ok1hra/IC-705_Interface/wifilt.ino

/*
  Based on ESP32 BT CAT for IC-705 by OK1CDJ ondra@ok1cdj.com
  https://github.com/ok1cdj/IC705-BT-CIV
  -----------------------------------------------------------
  This program is free software: you can redistribute it and/or modify
  it under the terms of the GNU General Public License as published by
  the Free Software Foundation, either version 3 of the License, or
  (at your option) any later version.
  This program is distributed in the hope that it will be useful,
  but WITHOUT ANY WARRANTY; without even the implied warranty of
  MERCHANTABILITY or FITNESS FOR A PARTICULAR PURPOSE.  See the
  GNU General Public License for more details.
  You should have received a copy of the GNU General Public License
  along with this program.  If not, see <http://www.gnu.org/licenses/>.
  -----------------------------------------------------------

  Firmware build dependencies
  - Arduino IDE 1.8.19 or 2.x
  - Espressif Arduino-ESP32 core 2.0.14
  - Board: "ESP32 Dev Module"
  - Partition Scheme: "No OTA (2MB APP/2MB SPIFFS)"
  - TrxNet 0.3.0: https://github.com/ok1hra/TrxNet
  EEPROM, BluetoothSerial, WiFi, ESPmDNS, WebServer, FS and LittleFS are
  supplied by the pinned ESP32 core; PubSubClient is not required.

  DATA/JS8 asset and release dependencies (Debian 12)
    sudo apt install build-essential ca-certificates cmake dpkg-dev emscripten \
      git gzip libboost1.81-dev libfftw3-dev nodejs p7zip-full python3 \
      terser xz-utils
  Enable matching Debian deb-src entries for the pinned FFTW source build.
  Reviewed release versions: Emscripten 3.1.6, CMake 3.25.1, Node 18.20.4
  (local checks accept Node 18-20). See docs/js8call-build.md.

  1. Increase REV value in this .ino
  2. Arduino IDE 1.8.19 menu: Sketch/Export compiled Binary (for "ESP32 Dev Module" + Tools/Partition Scheme:"No OTA (2MB APP/2MB SPIFFS)")
  3. ./tools/upload-firmware-spiffs.sh --port /dev/ttyUSB0
     check without write
     ./tools/upload-firmware-spiffs.sh --dry-run
    for slow comm
    ./tools/upload-firmware-spiffs.sh --port /dev/ttyUSB0 --baud 460800

  3. generate all .bin and publish to GitHub web page: $ ./tools/gh-pages.sh --publish
  4. git commit with comment Release number and push

  Manual workflow
  - afer standart edit data/*.html/css/js,
  - before manual filesystem upload run tools/gzip-assets.sh
  - continue with Arduino IDE

  Features
  + Three independently configured radio slots using LAN, TrxNet or CI-V
  + Frequency and mode for PHP log available on http port 81 (address http://wifilt.local:81)
  + UDP port 89 receives ascii characters and transmits them as a CW or RTTY message
  + UDP port 89 receives ascii characters, which it sends in RTTY mode by keying FSK and PTT TRX inputs
  + Status LED
    - Fade in/out - WiFi in AP mode
    - WiFi in client mode
      - ON waiting connected to WiFi
      - OFF Wifi connected to AP
      - FLASH send MQTT freq
      - DOUBLE FLASH receive CW via UDP
      - FLASH+PTT receive RTTY via UDP
  + mDNS - to easily find IP devices in the network, using the command "ping wifilt.local"
  + Watchdog - resets the device after more than 73 seconds of inactivity
  + Output signal POWER-OUT (13.8V/0.5A) with LED activates after connecting a full-CAT primary radio
  + Galvanically isolated CI-V output for connecting PA or other devices
  + CIV-MUTE on gpio16 allow send to CI-V output only commands with frequency (not debug messages)
  + UDP port for CAT command (clear RIT) from log
  + after a full-CAT primary connection, set TRX to enable CI-V transceive + RIT + BK-IN
  + support external shift register control switch by frequency (not tested)
  + Detect PCB hardware ID
  + postponed MQTT
  + legacy BT configuration retained only for downgrade compatibility
  + detect HW rev 02
  + after connect WiFi, play assigned IP address in CW on a full-CAT TRX1 as sidetone only (BK-IN forced off so it never transmits; snapshots+restores mode/BK-IN/AF/RF gain)
  + send ? in serial terminal, answer interface status
  + add AP mode - status LED signal AP mode by slowly turning on and off (fade in / fade out)
  + add setup http web form on port 80
  + add HW rev 3 detection
  + optional reset after diconnect
  + add Debug to CLI

  
  FYI https://github.com/Rhizomatica/mercury

//--------------------------------------------------------------------*/

String SSID         = "";
String PSWD         = "";
String SSID2        = "";
String PSWD2        = "";
// TrxNet config — NET_ID 0x00 = disabled sentinel (TrxNet not activated)
byte     TRXNET_ID      = 0x01;   // own device NET_ID → device name "705.01"
byte     TRX2_NET_ID    = 0xff;   // peer NET_ID for TRX2 Band Decoder slot (0x00 = disabled)
byte     TRX3_NET_ID    = 0x00;   // peer NET_ID for TRX3 Band Decoder slot (0x00 = disabled)
byte     TRX2_CONN_TYPE = 0x00;   // 0=TrxNet, 1=CI-V, 2=LAN (EEPROM byte 44)
byte     TRX3_CONN_TYPE = 0x00;   // 0=TrxNet, 1=CI-V, 2=LAN (EEPROM byte 47)
byte     TRX2_CIV_ADDR  = 0x00;   // CI-V address of TRX2 when CONN_TYPE=CI-V (EEPROM byte 48; 0x00=unset)
byte     TRX3_CIV_ADDR  = 0x00;   // CI-V address of TRX3 when CONN_TYPE=CI-V (EEPROM byte 49; 0x00=unset)
uint16_t TRXNET_PORT    = 5683;   // CoAP/discovery UDP port (CoAP default)
int BaudRate        = 9600;
// char* BTname        = "";
// const char* BTname  = "IC705-interface";
String BT_NAME;  // legacy EEPROM field, retained for downgrade compatibility
bool Debug          = false;
bool cwIpOnConnect  = true;       // announce WiFi IP via CW on first full-CAT radio connect
volatile bool cwIpSendPending = false;

#define LOOP_WARN_MS 200
#define REV 20260807
#define WIFI
#define UDP_TO_FSK
#define WDT         // watchdog timer
#define CIV_OUT     // send freq to CIV out with BaudRate
// #define BLUETOOTH   // legacy only; UI supports LAN, TrxNet and CI-V
// #define RTLE     // not work now | credit OK2CQR https://github.com/ok2cqr/rtle/tree/master
// #define RESET_AFTER_DISCONNECT  // enable reset after each disconnect + short CW msg

#include "EEPROM.h"
#define EEPROM_SIZE 360
/*
  0|Byte    1|128
  1|Char    1|A
  2|UChar   1|255
  3|Short   2|-32768
  5|UShort  2|65535
  7|Int     4|-2147483648
  11|Uint    4|4294967295
  15|Long    4|-2147483648
  19|Ulong   4|4294967295
  23|Long64  8|0x00FFFF8000FF4180
  31|Ulong64 8|0x00FFFF8000FF4180
  39|Float   4|1234.1234
  43|Double  8|123456789.12345679
  51|Bool    1|1

  0 APmode
  1-20 SSID1
  22-39 PSWD1
  41 TRXNET_ID       (own NET_ID, 0x00=disabled → device name "705.XX")
  42 TRX2_NET_ID     (peer NET_ID for TRX2 BD slot, 0x00=disabled)
  43 TRX3_NET_ID     (peer NET_ID for TRX3 BD slot, 0x00=disabled)
  44 TRX2_CONN_TYPE (0=TrxNet, 1=CI-V, 2=LAN; 0xff=unprogrammed → default 0x00)
  45-46 TRXNET_PORT  (was MQTT_PORT)
  47 TRX3_CONN_TYPE (0=TrxNet, 1=CI-V, 2=LAN; 0xff=unprogrammed → default 0x00)
  48 TRX2_CIV_ADDR  (CI-V address of TRX2; 0x00/0xff = unset)
  49 TRX3_CIV_ADDR  (CI-V address of TRX3; 0x00/0xff = unset)
  50 TRX1_CONFIG_MARKER (0xa5=current; 0xff=legacy memories.cfg fallback)
  51 TRX1_TRANSPORT  (1=LAN, 2=legacy Bluetooth, 3=CI-V, 4=TrxNet)
  52 TRX1_CIV_ADDR
  53-68 TRX1_LAN_IP (16B including 0xff terminator padding)
  69 FREE            (was HTTP_CAT_PORT)
  70-71 FREE         (was udpPort)
  72-73 FREE         (was udpCatPort)
  74-75 BaudRate
  76-95 SSID2
  97-114 PSWD2
  115-131 TRX1_LAN_USER (17B including 0xff terminator padding)
  132-135 FREE       (was MQTT_TOPIC_RX)
  136 cwIpOnConnect
  137-200 DXC host (64B)
  201-202 DXC port (UShort)
  203-218 DXC callsign (16B)
  219-224 DXC locator (6B)
  225-241 TRX1_LAN_PASSWORD (17B including 0xff terminator padding)
  242-245 FREE       (was TRX2 MQTT root topic)
  246-266 FREE       (was TRX3 MQTT root topic 21B)
  267-287 BT_NAME (21B)
  288 TRXNET_PRIO flag (0xff=unprogrammed → default "OI3 ANT"; 0x01=user set → read string)
  289-359 TRXNET_PRIO priority prefixes string (space-separated, 71B; empty = priority off)

  !! Increment EEPROM_SIZE #define !!
*/

#if defined(BLUETOOTH)
  #include "BluetoothSerial.h"
  #include <esp_bt.h>
#endif
  //#define DEBUG 1
  //#define MIRRORCAT 1
  //#define MIRRORCAT_SPEED 9600
  // CI-V protocol constants and radio state below are shared by every transport
  // (Bluetooth SPP and LAN both feed processCivBuffer), so they compile
  // unconditionally. Only the BluetoothSerial object is Bluetooth-specific.
  #define BROADCAST_ADDRESS    0x00 //Broadcast address
  #define CONTROLLER_ADDRESS   0xE0 //Controller address

  #define START_BYTE           0xFE //Start byte
  #define STOP_BYTE            0xFD //Stop byte

  #define CMD_TRANS_FREQ       0x00 //Transfers operating frequency data
  #define CMD_TRANS_MODE       0x01 //Transfers operating mode data

  #define CMD_READ_FREQ        0x03 //Read operating frequency data
  #define CMD_READ_MODE        0x04 //Read operating mode data

  #define CMD_WRITE_FREQ       0x05 //Write operating frequency data
  #define CMD_WRITE_MODE       0x06 //Write operating mode data

  #define CMD_SEND_CW_MSG      0x17 //Write operating mode data

  #define IF_PASSBAND_WIDTH_WIDE   0x01
  #define IF_PASSBAND_WIDTH_MEDIUM   0x02
  #define IF_PASSBAND_WIDTH_NARROW   0x03

  const uint32_t decMulti[]    = {1000000000, 100000000, 10000000, 1000000, 100000, 10000, 1000, 100, 10, 1};

  #define BAUD_RATES_SIZE 4
  const uint16_t baudRates[BAUD_RATES_SIZE]       = {19200, 9600, 4800, 1200};

  uint8_t  radio_address;     //Transiever address
  uint16_t  baud_rate;        //Current baud speed
  uint32_t readtimeout = 2000;
  uint8_t  read_buffer[12];   //Read buffer
  // uint8_t  read_buffer_snapshot[12];   //Buffer snapshot
  uint32_t  frequency;        //Current frequency in Hz
  uint32_t  frequencyTmp;        //Current frequency in Hz
  uint32_t  timer;

  const char* mode[] = {"LSB", "USB", "AM", "CW", "FSK", "FM", "WFM", "DV"};
  #define MODE_TYPE_LSB   0x00
  #define MODE_TYPE_USB   0x01
  #define MODE_TYPE_AM    0x02
  #define MODE_TYPE_CW    0x03
  #define MODE_TYPE_RTTY  0x04
  #define MODE_TYPE_FM    0x05
  #define MODE_TYPE_DV    0x17

  char modes[12] = "OFF";
  // btClientConnected stays declared unconditionally: state/status JSON reads it
  // even without Bluetooth (it simply remains false when BT is compiled out).
  volatile bool btClientConnected = false;
#if defined(BLUETOOTH)
  BluetoothSerial CAT;
#endif

short HardwareRev = 99;
const int HWidPin       = 34;  // analog
int HWidValue           = 0;

int pwmChannel          = 0; // Selects channel 0
int frequence           = 1000; // PWM frequency of 1 KHz
int resolution          = 8; // 8-bit resolution, 256 possible values

const int StatusPin     = 5;
const int PowerOnPin    = 4;
long powerTimer         = 0;
bool statusPower        = 0;
const int CIVmutePin    = 16;
bool TrxNeedSet         = 0;
bool TrxSetupDone       = false;
volatile bool btStateBroadcastPending = false;
volatile bool btDisconnectPending = false;
volatile bool btConnectPending = false;

#if defined(WDT)
  // 73 seconds WDT (WatchDogTimer)
  #include <esp_task_wdt.h>
  #define WDT_TIMEOUT 73
  long WdtTimer=0;
#endif

#if defined(WIFI)
  #include <WiFi.h>
  #include <esp_wifi.h>
  #include "esp_coexist.h"
  #include <FS.h>
  #include <LittleFS.h>
  #define HTTP_MAX_DATA_WAIT 1000
  #include <WebServer.h>
  #include <mbedtls/sha1.h>
  #include <lwip/sockets.h>   // raw select() to poll audio-WS writability (never block the loop)
  // #include <ETH.h>
  // int SsidPassSize = (sizeof(SsidPass)/sizeof(char *))/2; //array size
  // int SelectSsidPass = -1;
  #define wifi_max_try 40             // Number of try
  unsigned long WifiTimer = 0;
  unsigned long WifiReconnect = 5000;
  unsigned long WifiDownSince = 0;        // 0 = station link OK
  bool WifiHardResetDone = false;         // one radio off/on per outage — repeating it wedges the driver
  bool WifiCoexPreferred = false;         // coex arbiter tilted to WiFi for the duration of an outage
  #define WIFI_HARD_RESET_AFTER_MS 10000  // radio off/on cycle when down longer than this
  #define WIFI_RESTART_AFTER_MS    60000  // ESP.restart() when down longer than this
  // Last known AP — reconnect targets channel+BSSID directly, because a full
  // scan often finds nothing while the BT Classic (SPP) link is active (coex).
  int32_t wifiLastChannel = 0;
  uint8_t wifiLastBssid[6];
  bool    wifiLastBssidValid = false;
  String  wifiLastSsid;
  unsigned long webQuietUntil = 0;
  byte ActiveWifiProfile = 0;
  String MACString;

  #include <ESPmDNS.h>
  #include <DNSServer.h>

  const char* ssidAP     = "WIFILT-AP";
  const char* passwordAP = "remoteqth";
  // One name for three lookup paths: the DHCP hostname the router registers in
  // its own DNS (http://wifilt/), the mDNS name (http://wifilt.local) and the AP
  // captive portal. Keeping them identical is the whole point -- the operator
  // types one string no matter which mechanism their network actually supports.
  const char* deviceHostname = "wifilt";
  bool APmode = false;
  // WebServer discards the client before handleClient() returns, so the slow-loop
  // diagnostic can't sample it from outside. Response writes (where stalls to a dead
  // client block the loop) go through this virtual, so capture peer+uri here.
  class DiagWebServer : public WebServer {
  public:
    using WebServer::WebServer;
    IPAddress lastPeer;
    String lastUri;
  protected:
    size_t _currentClientWrite(const char* b, size_t l) override {
      if (_currentClient.connected()) {
        lastPeer = _currentClient.remoteIP();
        lastUri = _currentUri;
      }
      return WebServer::_currentClientWrite(b, l);
    }
  };
  DiagWebServer webServer(80);
  const byte DNS_PORT = 53;
  DNSServer dnsServer;             // captive portal in AP mode
#endif
  #if defined(RTLE)
    #ifndef HTTP_MAX_DATA_WAIT
      #define HTTP_MAX_DATA_WAIT 1000
    #endif
    #include <WebServer.h>
    #include "rtle.h"  //Web page header file
    WebServer rtleserver(88);
  #endif


// uint8_t CwMsg[36] = "";
char CwMsg[37] = "";

#if defined(UDP_TO_FSK)
  #define FSK_OUT  33                      // TTL LEVEL pin OUTPUT
  #define PTT      32                      // PTT pin OUTPUT
  #define FSK_MARK_LEVEL   LOW             // FSK mark level [LOW/HIGH]
  #define FSK_SPACE_LEVEL  HIGH            // FSK space level [LOW/HIGH]
  #define BaudRateFSK 45.45                   // RTTY baud rate
  #define StopBit  1.5                     // stop bit long
  #define PTTlead  400                     // PTT lead delay ms
  #define PTTtail  200                     // PTT tail delay ms
  int     OneBit = 1/BaudRateFSK*1000;
  boolean d1;
  boolean d2;
  boolean d3;
  boolean d4;
  boolean d5;
  boolean space;
  boolean fig1;
  int     fig2;
  char    ch;
  volatile bool abortFskTransmission = false;
#endif


// TrxNet — P2P telemetry, replaces PubSubClient/MQTT
// TRXNET_ID == 0x00 acts as "disabled" sentinel — net.begin() is not called.
// NOTE: never #define TRXNET_MAX_PENDING/TRXNET_MAX_PEERS here — TrxNet.cpp is
// compiled separately without sketch defines, so the class layout would differ
// between translation units (ODR violation → global memory corruption → boot
// crash in first nvs_open). Library per-board defaults apply (ESP32: 24).
#include <WiFiUdp.h>
#include <TrxNet.h>
#include "icomLanClient.h"      // LAN CI-V transport (alternative to BT)
#include "radio_transport.h"    // shared per-slot transport/capability model
#include "aud1_tx_state.h"      // shared TX-state predicates used by native regression tests
#include "unattended_guard.h"   // shared liveness/arming rules used by native regression tests
#include "unattended_events.h"  // shared event-log formatting used by native regression tests
#include "aud1_ws_parser.h"     // incremental, non-blocking browser WebSocket framing
#include "js8_session.h"        // single-operator lock for the JS8LAN page
IcomLanClient lanClient;
IcomLanClient* secondaryLanClients[2] = {nullptr, nullptr};
bool    lanMode = true;         // compatibility mirror: TRX1 transport == LAN
String  lanRadioIp = "";        // radio IP for LAN mode
String  lanUser = "";           // ICOM network username
String  lanPass = "";           // ICOM network password
uint32_t lanFreqTmp = 0;        // last freq published to TrxNet (change detect)
bool    lanReconnectRequested = false;
uint32_t lanRetryAt = 0;
uint32_t lanBackoff = 3000;

// ---- LAN radio discovery (SETUP page) -------------------------------------
// The scanner and the credential test both need UDP 50001, which the live LAN
// client owns. WiFiUDP sets SO_REUSEADDR, so a second bind succeeds and then
// silently steals the client's control packets -- the live client is therefore
// stopped for the duration and reconnected afterwards, never run alongside.
#include "icom_lan_discovery.h"
IcomLanDiscovery icomScan;
enum IcomScanPhase : uint8_t {
  ISCAN_IDLE, ISCAN_SUSPEND, ISCAN_RUN,
  ISCAN_TEST_SUSPEND, ISCAN_TEST_RUN,
  ISCAN_DONE
};
IcomScanPhase icomScanPhase = ISCAN_IDLE;
bool     icomScanSuspendLan = false;   // gate honoured by the LAN service loops
bool     icomScanLanWasUp = false;     // reconnect afterwards only if we cut it
bool     icomScanFailed = false;       // scan could not start (no station link)
IcomLanClient* icomTestClient = nullptr;
IPAddress icomTestIp;
String   icomTestUser, icomTestPass;
uint8_t  icomTestCivAddr = 0xA4;
uint8_t  icomTestSlot = 0;             // which TRX slot the tested address belongs to
String   icomTestModel;                // model the radio reported during the test
uint32_t icomTestDeadline = 0;
const char* icomTestResult = "idle";   // idle|running|ok|bad_credentials|no_answer

// ---- AP -> station handoff --------------------------------------------------
// Saving WiFi credentials in AP mode used to end with a blind restart: the
// portal vanished and the operator was left with no address to open. Instead
// the station is brought up alongside the still-running softAP, so the portal
// can show the address the router actually handed out before the AP goes away.
#define LAST_STA_IP_ADDR 132       // EEPROM 132-135, previously MQTT_TOPIC_RX
// One configured WiFi profile as the scan actually saw it on the air.
struct WifiScanPick {
  byte    profile = 0xFF;
  int32_t rssi = -127;
  int32_t channel = 0;
  uint8_t bssid[6] = {0};
  bool    targeted = false;   // false = no scan hit, connect the ordinary way
};
enum WifiTryState : uint8_t { WTRY_IDLE, WTRY_SCAN, WTRY_CONNECTING, WTRY_OK, WTRY_FAILED };
WifiTryState wifiTryState = WTRY_IDLE;
uint32_t  wifiTryDeadline = 0;
String    wifiTrySsid;
const char* wifiTryReason = "";    // not_found | no_connect, when state == failed
WifiScanPick wifiTryCandidates[2]; // profiles to attempt, strongest scan hit first
uint8_t   wifiTryCandidateCount = 0;
uint8_t   wifiTryCandidateIdx = 0;
bool      wifiTryScanSawNothing = false;  // a scan completed and found no configured SSID
IPAddress lastStaIp;               // survives a reboot; 0.0.0.0 when unknown

static const char* RADIO_CONFIG_PATH = "/radio-config.json";

struct RadioSlotConfig {
  bool enabled;
  RadioTransport transport;
  uint8_t civAddr;
  uint8_t netId;
  String lanIp;
  String lanUser;
  String lanPass;
  // Model the radio reported in its capabilities packet, remembered across
  // reboots. Not operator-editable -- it is an observation, not a setting.
  // WSPR needs it to know whether 100 % of the CI-V power scale means 10 W or
  // 100 W, and without a stored copy that answer disappears with the link.
  String model;
};

RadioSlotConfig radioSlots[3];
bool radioConfigLoaded = false;
bool primarySerialHasData = false;
bool primaryTrxNetHasData = false;
uint32_t secondaryLanRetryAt[2] = {0, 0};
uint32_t secondaryLanBackoff[2] = {3000, 3000};

// ── The LAN radio, wherever the operator put it ───────────────────────────────
// LAN may be assigned to any one of the three slots, and JS8LAN (audio, PTT, TX)
// follows it instead of assuming TRX1. The shared CAT globals (frequency, modes,
// stateTx, meters) belong to TRX1 -- /state, the log page's TRX1 tab, band
// decoder source 1 and the TrxNet publish all read them -- so a LAN radio in
// slot 1 or 2 keeps its own compact snapshot here and the JS8 page asks for it
// with /state?radio=lan. Only one slot can be LAN, hence one snapshot.
struct LanRadioSnapshot {
  uint8_t  slot = 0xFF;           // which slot this snapshot describes
  bool     tx = false;
  uint8_t  filter = 0;
  uint8_t  rfPower = 0;
  bool     rfPowerSeen = false;   // false until the radio answered 14 0A at least once
  uint16_t smeterRaw = 0;
  uint16_t powerMeterRaw = 0;
  // Raw ALC, and a counter that only moves when the radio actually answered
  // 15 13. The browser's gain search cannot tell a fresh reading from the
  // previous one repeated -- and mistaking one for the other makes it step
  // twice on a single observation -- so the sequence, not the value, is what
  // says "this is new". Deliberately absent from /state: it is only meaningful
  // while the browser is keying, and that is exactly when tx-level is flowing.
  uint16_t alcRaw = 0;
  uint32_t alcSeq = 0;
  float    swr = 1.0f;
  float    supplyVolts = 0.0f;
  char     mode[8] = "";          // includes the -D suffix, unlike g_trxMode
};
LanRadioSnapshot lanRadioSnap;
WiFiUDP trxUdp;
TrxNet  net(trxUdp);
char    trxDeviceName[TRXNET_MAX_DEVICE_NAME];
bool    trxNetEnabled = false; // set true after net.begin() succeeds

// TrxNet priority prefixes — protect these peers when the peer table fills.
// EEPROM 288 flag + 289-359 string. Limits: 8 tokens x 8 chars (see setPriorityPrefixes()).
#define TRXNET_PRIO_MAX_TOKENS 8
#define TRXNET_PRIO_MAX_TOKLEN 8
#define TRXNET_PRIO_STR_MAX    71   // 8*8 + 7 separators
String      TRXNET_PRIO = "OI3 ANT";                 // canonical (normalized) value for UI/save
char        trxPrioBuf[TRXNET_PRIO_STR_MAX + 1];     // tokenized: spaces -> '\0' (library holds a pointer)
const char* trxPrioPtrs[TRXNET_PRIO_MAX_TOKENS];     // pointers into trxPrioBuf, valid for object lifetime
uint8_t     trxPrioCount = 0;

// TrxNet pending state — set in callbacks, processed in loop()
volatile uint32_t trxPendingHz   = 0;
volatile uint8_t  trxPendingMode = 0; // CI-V byte
volatile bool     trxFreqPending = false;
volatile bool     trxModePending = false;

int incomingByte = 0;   // for incoming serial data

#if defined(WIFI)
  WiFiServer dxcRawServer(82);
  WiFiClient DxcTelnetClient;
  WiFiClient DxcWsClient;
  WiFiServer audioWsServer(83);        // AUD1 WebSocket: timed RX/TX audio for DATA page
  WiFiClient AudioWsClient;
  uint32_t audioRxPackets = 0;         // counts forwarded audio datagrams per WS session
  uint8_t  audioTxBuf[1400];           // coalesce ~20ms radio packets into fewer WS frames
  size_t   audioTxLen = 0;
  // Outgoing browser-WS byte ring. RX audio is enqueued here (even from the LAN
  // UDP receive path) and drained with non-blocking ::send, so no WS write ever
  // blocks the cooperative loop and the LAN-UDP owner never performs a socket
  // send. ~2 s at 8 kB/s absorbs transient browser/WiFi stalls before dropping.
  // Heap-allocated in setup() — too large for the static DRAM (.bss) segment.
  static const size_t WS_OUT_SIZE = 16384;
  uint8_t* wsOut = nullptr;
  size_t   wsOutHead = 0, wsOutTail = 0, wsOutLen = 0;
  bool     audioTxKeyed = false;       // M3: PTT keyed for browser-sourced TX audio
  bool     audioPttOffPending = false; // desired OFF not yet submitted to healthy CI-V
  uint32_t audioPttRetryAt = 0;
  uint32_t audioTxLastMs = 0;          // last TX audio/keep-alive — dead-man un-key timer
  uint32_t audioStreamId = 0;          // changes for every WebSocket media epoch
  uint32_t audioRxSequence = 0;
  uint64_t audioRxFirstSample = 0;
  bool audioRxFirst = true;
  bool audioRxDiscontinuity = false;
  bool audioRadioSequenceValid = false;
  uint16_t audioRadioExpectedSequence = 0;

  Aud1TxState aud1TxState = AUD1_TX_IDLE;
  static const size_t AUD1_TX_RING_SIZE = IcomLanAudioTx::QUEUE_CAPACITY;
  size_t aud1TxUsed = 0;                    // atomic snapshot mirror for UI/state JSON
  uint32_t aud1TxId = 0, aud1TxExpectedSequence = 0, aud1TxExpectedPackets = 0;
  uint32_t aud1TxReceivedPackets = 0, aud1TxTargetMs = 0;
  uint32_t aud1TxDeadlineMs = 0, aud1TxPrebufferSamples = 0;
  uint64_t aud1TxExpectedSample = 0, aud1TxTotalSamples = 0, aud1TxConsumedUlaw = 0;
  bool aud1TxLastSeen = false;
  Aud1WsParser aud1WsParser;
  UnattendedGuard unattendedGuard;
  Js8Session js8Session;                   // which browser currently owns JS8LAN
  static const char* UNATTENDED_LOG_PATH = "/unattended.log";
  // Deferred unattended-log ring. unattendedLogEvent() is called from the audio
  // hot path (aud1TxAbort/aud1TxTick/aud1HandleControl); a synchronous LittleFS
  // append+rotate there is a multi-100 ms flash stall that can miss the very next
  // JS8 slot. Events are formatted into this RAM ring instead and flushed to flash
  // only from loop() while no TX is imminent (unattendedLogFlush). Heap-allocated
  // like wsOut; if malloc fails, the hot path records an overflow marker and
  // still never falls back to a synchronous flash write during TX.
  static const size_t UNA_LOG_QUEUE_SIZE = 2048;   // ~17 lines of <=120 B
  uint8_t* unaLogQueue = nullptr;
  size_t   unaLogHead = 0, unaLogTail = 0, unaLogLen = 0;
  bool     unaLogOverflow = false;                 // oldest lines dropped since last flush
  // MSG BOX: store-and-forward mail, unread mail for the operator and our own
  // deferred outgoing messages, one typed record per line. Decision 10 keeps it
  // here rather than in the tab so it survives a reload, a different computer
  // and a cleared browser cache, and can be read from a phone. 96 messages x
  // ~120 chars fits well inside the 256 KiB runtime reserve the deployment gate
  // keeps free.
  static const char* MSGBOX_PATH = "/msgbox.jsonl";
  // Pre-type file. Read once so mail survives the upgrade, then removed; the
  // browser is what knows how to tell the old record kinds apart.
  static const char* MSGBOX_LEGACY_PATH = "/inbox.jsonl";
  static const size_t MSGBOX_MAX_BYTES = 24576;
  bool lanLinkWasUp = false;               // LAN link-up edge for the PTT safety un-key
  uint32_t aud1TxLevelNextMs = 0;          // B3: periodic TX buffer level while streaming
  // Survives a WDT/panic reset (not power loss) so a reset that happened with
  // the radio keyed is reportable instead of silent.
  RTC_NOINIT_ATTR uint32_t rtcPttWasKeyed;
  static const size_t AUD1_WS_RX_BYTE_BUDGET = 32768; // yield even when browser continuously streams
  static const uint32_t AUD1_WS_SLOT_BACKLOG_GRACE_MS = 100;
  String DxcHost = "";
  uint16_t DxcPort = 7300;
  IPAddress DxcHostIp;                // cached resolve — hostByName blocks the loop for seconds
  String DxcHostResolved = "";        // host the cache belongs to
  #define DXC_CONNECT_TIMEOUT_MS 1500
  String DxcCallsign = "";
  String DxcLocator = "";

  static const char* LOG_CONFIG_PATH = "/log-config.json";

  // Measured ALC knees, one entry per model|band|percent. Deliberately opaque
  // to the firmware: it serves the file and overwrites it, and never parses a
  // byte of it. The schema belongs to the browser, which is the only party that
  // can decide what a calibration means -- and a parser here would be a second
  // opinion about it, needing RAM, a version field and a migration path for a
  // table the radio itself has no use for.
  //
  // Firmware-side rather than in localStorage because the knee is a property of
  // the station -- radio, band, power -- not of the browser that measured it. An
  // unattended beacon started from a phone must not transmit at a level that was
  // only ever calibrated on the shack PC.
  static const char* TXGAIN_CONFIG_PATH = "/txgain.json";
  static const size_t TXGAIN_MAX_BYTES = 6144;   // ~40 entries; a full band plan

  // In-memory cache of log-config.json fields used by setupTemplateProcessor.
  String g_lcTrx1Label = "TRX1";   // replaced by the radio's own model once known
  String g_lcTrx2Label = "TRX2";
  String g_lcTrx3Label = "TRX3";
  String g_lcRstSsb    = "59";
  String g_lcRstCwRtty = "599";
  bool   g_lcManualModeForPhone = true;
  String g_lcBlockedDxcc = "Russia\nBelarus\nKaliningrad";

  // TrxNet peer cache for TRX2 (index 0) and TRX3 (index 1) — written by onHz/onMode callbacks
  static volatile long g_trxFreq[2]    = {0, 0};
  static char          g_trxMode[2][8] = {"USB", "USB"};
  static volatile bool g_trxHasData[2] = {false, false};

// Band Decoder
#define BD_CLOCK_PIN  15
#define BD_LATCH_PIN  13
#define BD_DATA_PIN   14
#define BD_ROWS       16
#define BD_CONFIG_PATH "/bd-config.json"

struct BdRow {
    uint32_t fMin;
    uint32_t fMax;
    uint16_t outputs;
};

BdRow     bdRows[BD_ROWS];
int       bdSource         = 1;
uint16_t  bdCurrentOutputs = 0;
bool      bdEnabled        = false;

  bool DxcTelnetStatus = false;
  bool DxcWsStatus = false;
  bool DxcTelnetLoginPending = false;
  unsigned long DxcReconnectTimer = 0;
#endif

#if defined(WIFI)
typedef mbedtls_sha1_context SHA1_CTX;

extern "C" void SHA1Init(SHA1_CTX* context){
  mbedtls_sha1_init(context);
  mbedtls_sha1_starts_ret(context);
}

extern "C" void SHA1Update(SHA1_CTX* context, const unsigned char* data, uint32_t len){
  mbedtls_sha1_update_ret(context, data, len);
}

extern "C" void SHA1Final(unsigned char digest[20], SHA1_CTX* context){
  mbedtls_sha1_finish_ret(context, digest);
  mbedtls_sha1_free(context);
}
#endif

#if defined(WIFI)
  const uint8_t CW_MEMORY_COUNT = 4;
  const uint8_t FREQ_MEMORY_COUNT = 10;
  const size_t CW_MEMORY_MAX_LEN = 30;
  const size_t FREQ_MEMORY_MAX_LEN = 20;
  const uint8_t CIV_ADDRESS_DEFAULT = 0xA4;
  const char *MEMORY_CONFIG_PATH = "/memories.cfg";
  const uint8_t PRIMARY_RADIO_CONFIG_MARKER = 0xA5;
  const int PRIMARY_RADIO_MARKER_ADDR = 50;
  const int PRIMARY_RADIO_TRANSPORT_ADDR = 51;
  const int PRIMARY_RADIO_CIV_ADDR = 52;
  const int PRIMARY_RADIO_LAN_IP_ADDR = 53;
  const int PRIMARY_RADIO_LAN_USER_ADDR = 115;
  const int PRIMARY_RADIO_LAN_PASS_ADDR = 225;
  // BT CAT poll cadence (used by pollRadio) — slow when idle, fast while the
  // CAT page holds it via /state?fast=1
  #define CAT_POLL_MS       1000  // slow: freq poll interval
  #define CAT_MODE_EVERY    2     // slow: mode polled every N-th freq tick (2 s)
  #define AUX_POLL_MS       160   // slow: aux round-robin step (each of 10 items every 1.6 s)
  #define CAT_POLL_FAST_MS  200   // fast: freq+mode poll interval (original cadence)
  #define AUX_POLL_FAST_MS  80    // fast: aux round-robin step
  #define CAT_FAST_HOLD_MS  3000  // fast mode lingers this long after the last ?fast=1 poll
  #define CAT_POLL_OUTAGE_MS 3000 // WiFi outage: freq-only poll — BT must go near-silent
                                  // so the SPP link can sniff and WiFi can re-associate
  unsigned long catFastUntil = 0;
  String setupSsidErr = "";
  String setupPswdErr = "";
  String setupSsid2Err = "";
  String setupPswd2Err = "";
  String setupCivAddrErr = "";
  bool setupSaveOk = false;
  String transceiverType = "ICOM-LAN";  // LAN is the recommended default (BT deprecated)
  uint8_t configuredCivAddress = CIV_ADDRESS_DEFAULT;
  String cwMemoryText[CW_MEMORY_COUNT];
  String freqMemoryText[FREQ_MEMORY_COUNT];
  portMUX_TYPE stateMux = portMUX_INITIALIZER_UNLOCKED;

  // State variables updated from CIV frames, served via /state polling
  uint32_t stateRitRaw = 0;
  uint8_t stateFilter = 1;
  uint8_t stateAfGain = 0;
  uint8_t stateKeySpeed = 138;
  // 205 is a fabricated default, not a reading. Pages that turn the level into
  // watts must not present it as one, so say plainly whether the radio has ever
  // answered 14 0A -- the snapshot below carries the same flag for TRX2/TRX3,
  // where the equally fabricated default is 0.
  uint8_t stateRfPower = 205;
  bool stateRfPowerSeen = false;
  bool stateTx = false;
  uint8_t statePreampMode = 0;  // 0=OFF, 1=AMP, 2=ATT
  uint8_t stateAttOn = 0;       // internal: tracks ATT separately for combine logic
  uint8_t stateVoxMode = 0;
  uint8_t stateRfGain = 0;      // 0x14 0x02 RF gain, needed to snapshot/restore around CW IP announce
  uint8_t stateModeId = 0x03;   // numeric operating-mode id (0x03=CW), for exact mode restore
  bool    stateDataMode = false;// DATA sub-mode flag, so USB-D/etc. restore correctly
  float stateSupplyVolts = 0.0f;
  float stateSwr = 1.0f;
  uint32_t stateSmeterRaw = 0;
  uint32_t statePowerMeterRaw = 0;
  // TRX1's ALC, with the same freshness counter as the snapshot's. Two copies
  // because a LAN radio on TRX1 feeds the shared CAT globals and never the
  // snapshot -- see lanCivFrameRoute(), which returns early for slot 0.
  uint32_t stateAlcRaw = 0;
  uint32_t stateAlcSeq = 0;

  // civ.read: the one CI-V reply a page asked for, kept as RAW HEX. Nothing here
  // decodes it -- the same discipline as /txgain.json, which this firmware stores
  // and never parses. A settings value like 1A 05 01 17 is BCD on one model and
  // an enumeration on the next, so the only honest place for the meaning is the
  // page that asked. Zero RAM for a parser, and no model knowledge in C++.
  //
  // Absence is the answer for an address the radio does not have: no reply means
  // civReadSeq never moves, and the caller reports "the radio did not confirm
  // that address" instead of writing to it. See docs/tx-audio-gain-plan-*.md.
  static const size_t CIV_READ_MAX = 16;
  uint8_t  civReadPrefix[CIV_READ_MAX] = {0};   // cmd + subaddress bytes to match
  uint8_t  civReadPrefixLen = 0;
  uint8_t  civReadReply[CIV_READ_MAX] = {0};   // cmd + payload of the matching frame
  uint8_t  civReadReplyLen = 0;
  uint32_t civReadSeq = 0;
  uint32_t civReadAtMs = 0;

  String requestArg(const char *name);
  bool requestHasArg(const char *name);
  String trimMemoryValue(const String &value, size_t maxLen);
  bool parseHexByteString(const String &value, uint8_t &outValue);
  void loadMemoryConfig(void);
  bool saveMemoryConfig(void);
  bool hasPrimaryRadioConfig(void);
  void loadPrimaryRadioConfig(void);
  bool savePrimaryRadioConfig(void);
  void initLegacyRadioSlots(void);
  bool loadRadioConfig(void);
  bool saveRadioConfig(void);
  void syncLegacyRadioGlobals(void);
  bool radioSlotConnected(uint8_t slot);
  void radioSlotSetFrequencyState(uint8_t slot, uint32_t freq);
  void radioSlotSetModeState(uint8_t slot, const char *mode);
  IcomLanClient* radioLanClient(uint8_t slot);
  bool beginRadioLanClient(uint8_t slot);
  void secondaryLanClientsLoop(void);
  uint8_t lanRadioSlotIndex(void);
  String defaultTrxLabel(uint8_t slot);
  void adoptModelAsLabelIfUnset(uint8_t slot);
  IcomLanClient* lanRadioClient(void);
  bool lanRadioConnected(void);
  bool lanRadioSendCommand(const uint8_t *body, size_t len);
  bool lanRadioSendPriorityCommand(const uint8_t *body, size_t len, IcomLanClient::CivPriority priority);
  void lanRadioAudioService(IcomLanClient *client);
  void lanRadioCivSnapshot(const uint8_t *frame, size_t len);
  void lanCivFrameRoute(uint8_t slot, const uint8_t *frame, size_t len);
  String jsonEscape(const String &value);
  String configJsonEscape(const String &s);
  String civFrameToHex(const uint8_t *frame, size_t frameLen);
  uint32_t decodeCivFrequencyBytes(const uint8_t *bytes, size_t byteCount);
  uint32_t decodeCivBcdBytes(const uint8_t *bytes, size_t byteCount);
  String decodeModeName(uint8_t modeId);
  bool catWriteFrame(const uint8_t *frame, size_t frameLen, bool broadcastTx);
  bool catWriteFrameSlot(uint8_t slot, const uint8_t *frame, size_t frameLen);
  void setModesText(const char *value);
  void copyModesText(char *dest, size_t destSize);
  bool applyModeState(uint8_t modeId, bool dataMode);
  String extractJsonString(const String &json, const char *key);
  String extractJsonObject(const String &json, const char *key);
  bool extractJsonBool(const String &json, const char *key, bool defaultValue);
  bool parseHexPayload(const String &hex, uint8_t *buffer, size_t &bufferLen, size_t maxLen);
  bool parseModeId(const String &modeName, uint8_t &modeId);
  uint8_t parseFilterWidth(const String &filterName);
  size_t buildSimpleCatFrame(uint8_t command, const uint8_t *payload, size_t payloadLen, uint8_t *frame, size_t frameMaxLen);
  size_t buildSetFrequencyFrame(uint32_t freqHz, uint8_t *frame, size_t frameMaxLen);
  size_t buildSetModeFrame(uint8_t modeId, uint8_t modeWidth, uint8_t *frame, size_t frameMaxLen);
  size_t buildReadQuickSplitFrame(uint8_t *frame, size_t frameMaxLen);
  void buildStateJson(char *buf, size_t bufSize, bool lanView);
  void handleGetState(void);
  bool sendTemplatedHtml(const char *path);
  void handleSetupData(void);
  void handleTrxNetPeers(void);
  void handleWebServerLoop(void);
  bool handleFileFromSPIFFS(const String &path);
  void handlePostCmd(void);
  void handleSet(void);
  void renderSetupPage(void);
  void resetSetupMessages(void);
  String setupTemplateProcessor(const String &key);
  void setupWebServer(void);
  void handleConfigDownload(void);
  void handleConfigUpload(void);
  void handleGetLogConfig(void);
  void handlePostLogConfig(void);
  void handleGetTxGain(void);
  void handlePostTxGain(void);
  void handleGetCivRead(void);
  void civReadArm(const uint8_t *prefix, size_t prefixLen);
  void civReadCapture(const uint8_t *frame, size_t len);
  void handleOi3State(void);
  void handleOi3Send(void);
  void handleOi3SetHz(void);
  void TrxNetLoop(void);
  void onTrxHz(const char* from, const uint8_t* data, size_t len);
  void onTrxMode(const char* from, const uint8_t* data, size_t len);
  void onTrxSetHz(const char* from, const uint8_t* data, size_t len);
  static const char* trxnetModeToString(uint8_t civMode);
  void lanSecondaryCivFrameHandler(uint8_t slot, const uint8_t *frame, size_t len);
  static void civSend(uint8_t toAddr, const uint8_t* body, size_t bodyLen);
  void DxcLoop(void);
  void dxcHandleRawClient(void);
  bool DxcConfigReady(void);
  void DxcDisconnectTelnet(void);
  void DxcDisconnectWebSocket(void);
  void DxcRequestReconnect(void);
  void DxcUpdateTelnetStatus(bool connected, bool forceSend = false);
  void DxcSendTelnetStatus(void);
  bool DxcConnectTelnet(void);
  bool WiFiStationReady(void);
  void WiFiRetryActiveProfile(const char *reason);
  bool DxcSendWebSocketFrame(uint8_t opcode, const uint8_t* payload, size_t length);
  bool DxcSendWebSocketText(const char* text);
  bool DxcSendWebSocketText(const String& text);
  bool DxcHandleWebSocketUpgrade(WiFiClient& webClient, const String& request);
  void DxcHandleWebSocketClient(void);
  void DxcHandleTelnetClient(void);
  String ExtractHttpHeader(const String& request, const String& headerName);
  String DxcComputeWebSocketAccept(const String& secKey);
  String Base64Encode(const uint8_t* data, size_t length);
  bool AudioSendBinary(const uint8_t* payload, size_t length);
  bool AudioSendText(const String& text);
  void wsRingReset(void);
  void audioDrainWs(void);
  void audioFlush(void);
  void audioPttOn(void);
  void audioPttOff(void);
  void audioPttSafetyOnLink(void);
  void audioPttSafetyRetryTick(void);
  void unattendedLogEvent(uint8_t type, const String& detail);
  void unattendedLogEnqueue(const char* line, size_t n);
  void unattendedLogFlush(void);
  bool txCriticalNow(void);
  bool txRealtimeNow(void);
  void handleUnattendedGet(void);
  void handleUnattendedPost(void);
  void handleUnattendedLog(void);
  void js8SessionRespond(Js8SessionResult result, const String& token);
  String js8SessionRequestToken(void);
  void handleJs8SessionGet(void);
  void handleJs8SessionClaim(void);
  void handleJs8SessionPing(void);
  void handleJs8SessionRelease(void);
  void handleMsgboxGet(void);
  void handleMsgboxPost(void);
  void aud1TxAbort(const String& reason, bool notify = true);
  void aud1TxTick(bool deferPrebufferMiss = false);
  void AudioDisconnectWs(void);
  bool AudioHandleWsUpgrade(WiFiClient& webClient, const String& request, const String& token);
  void AudioHandleWsClient(void);
  void audioHandleRawClient(void);
#endif

//-------------------------------------------------------------------------------------------------------

#if defined(WIFI)
String requestArg(const char *name){
  return webServer.arg(name);
}

bool requestHasArg(const char *name){
  return webServer.hasArg(name);
}

String trimMemoryValue(const String &value, size_t maxLen){
  String trimmed = value;
  trimmed.trim();
  if (trimmed.length() > maxLen) {
    trimmed = trimmed.substring(0, maxLen);
    trimmed.trim();
  }
  return trimmed;
}

bool parseHexByteString(const String &value, uint8_t &outValue){
  String normalized = value;
  normalized.trim();
  normalized.toUpperCase();
  if (normalized.startsWith("0X")) {
    normalized = normalized.substring(2);
  }
  if (normalized.length() == 0 || normalized.length() > 2) {
    return false;
  }

  char buffer[3] = {0, 0, 0};
  normalized.toCharArray(buffer, sizeof(buffer));
  char *endPtr = nullptr;
  long parsed = strtol(buffer, &endPtr, 16);
  if (endPtr == nullptr || *endPtr != '\0' || parsed < 0 || parsed > 255) {
    return false;
  }
  outValue = (uint8_t)parsed;
  return true;
}

void loadMemoryConfig(void){
  for (uint8_t i = 0; i < CW_MEMORY_COUNT; i++) {
    cwMemoryText[i] = "";
  }
  for (uint8_t i = 0; i < FREQ_MEMORY_COUNT; i++) {
    freqMemoryText[i] = "";
  }

  if (!LittleFS.exists(MEMORY_CONFIG_PATH)) {
    return;
  }

  File file = LittleFS.open(MEMORY_CONFIG_PATH, FILE_READ);
  if (!file) {
    return;
  }

  for (uint8_t i = 0; i < CW_MEMORY_COUNT && file.available(); i++) {
    cwMemoryText[i] = trimMemoryValue(file.readStringUntil('\n'), CW_MEMORY_MAX_LEN);
  }
  for (uint8_t i = 0; i < FREQ_MEMORY_COUNT && file.available(); i++) {
    freqMemoryText[i] = trimMemoryValue(file.readStringUntil('\n'), FREQ_MEMORY_MAX_LEN);
  }

  if (file.available()) {
    String configuredType = trimMemoryValue(file.readStringUntil('\n'), 16);
    if (configuredType == "IC-7610-CI-V" || configuredType == "TRXNET") {
      transceiverType = configuredType;
    } else {
      // Bluetooth transport removed: any stored non-CIV value falls back to LAN.
      transceiverType = "ICOM-LAN";
    }
  }

  if (file.available()) {
    uint8_t parsedAddress = CIV_ADDRESS_DEFAULT;
    if (parseHexByteString(file.readStringUntil('\n'), parsedAddress)) {
      configuredCivAddress = parsedAddress;
    }
  }

  // LAN transport config (backward compatible: absent lines -> empty)
  if (file.available()) lanRadioIp = trimMemoryValue(file.readStringUntil('\n'), 15);
  if (file.available()) lanUser    = trimMemoryValue(file.readStringUntil('\n'), 16);
  if (file.available()) lanPass    = trimMemoryValue(file.readStringUntil('\n'), 16);

  lanMode = (transceiverType == "ICOM-LAN");

  file.close();
}

bool saveMemoryConfig(void){
  File file = LittleFS.open(MEMORY_CONFIG_PATH, "w");
  if (!file) {
    Serial.println("LFS | cannot open /memories.cfg for writing"
                   " used=" + String(LittleFS.usedBytes()) +
                   " total=" + String(LittleFS.totalBytes()));
    return false;
  }

  size_t expectedBytes = 0;
  size_t writtenBytes = 0;
  auto writeLine = [&](const String &line) {
    expectedBytes += line.length() + 2;  // println uses CRLF
    writtenBytes += file.println(line);
  };

  for (uint8_t i = 0; i < CW_MEMORY_COUNT; i++) {
    writeLine(trimMemoryValue(cwMemoryText[i], CW_MEMORY_MAX_LEN));
  }
  for (uint8_t i = 0; i < FREQ_MEMORY_COUNT; i++) {
    writeLine(trimMemoryValue(freqMemoryText[i], FREQ_MEMORY_MAX_LEN));
  }
  writeLine(transceiverType);
  String civAddressLine;
  if (configuredCivAddress < 16) {
    civAddressLine = "0";
  }
  civAddressLine += String(configuredCivAddress, HEX);
  writeLine(civAddressLine);
  writeLine(lanRadioIp);
  writeLine(lanUser);
  writeLine(lanPass);

  file.flush();
  size_t fileBytes = file.size();
  bool ok = writtenBytes == expectedBytes && fileBytes == expectedBytes;
  file.close();
  if (!ok) {
    Serial.println("LFS | write failed for /memories.cfg expected=" +
                   String(expectedBytes) + " written=" + String(writtenBytes) +
                   " size=" + String(fileBytes) +
                   " used=" + String(LittleFS.usedBytes()) +
                   " total=" + String(LittleFS.totalBytes()));
  }
  return ok;
}

// Parse log-config.json into g_lc* variables so setupTemplateProcessor can serve them.
void loadLogConfigVars(void){
  if (!LittleFS.exists(LOG_CONFIG_PATH)) return;
  File f = LittleFS.open(LOG_CONFIG_PATH, "r");
  if (!f) return;
  String j = f.readString();
  f.close();
  j.trim();
  if (!j.startsWith("{")) return;

  String v;
  v = extractJsonString(j, "trx1Label"); if (v.length() > 0) g_lcTrx1Label = v;
  v = extractJsonString(j, "trx2Label"); if (v.length() > 0) g_lcTrx2Label = v;
  v = extractJsonString(j, "trx3Label"); if (v.length() > 0) g_lcTrx3Label = v;
  v = extractJsonString(j, "rstSsb");    if (v.length() > 0) g_lcRstSsb = v;
  v = extractJsonString(j, "rstCwRtty"); if (v.length() > 0) g_lcRstCwRtty = v;
  if (j.indexOf("\"blockedDxcc\"") >= 0) g_lcBlockedDxcc = extractJsonString(j, "blockedDxcc");
  g_lcManualModeForPhone = extractJsonBool(j, "manualModeForPhone", true);
}

String jsonEscape(const String &value){
  String out;
  out.reserve(value.length() + 8);
  for (size_t i = 0; i < value.length(); i++) {
    char c = value.charAt(i);
    switch (c) {
      case '\\': out += "\\\\"; break;
      case '"': out += "\\\""; break;
      case '\n': out += "\\n"; break;
      case '\r': out += "\\r"; break;
      case '\t': out += "\\t"; break;
      default: out += c; break;
    }
  }
  return out;
}

String civFrameToHex(const uint8_t *frame, size_t frameLen){
  String hex;
  hex.reserve(frameLen * 2);
  for (size_t i = 0; i < frameLen; i++) {
    if (frame[i] < 16) {
      hex += "0";
    }
    hex += String(frame[i], HEX);
  }
  return hex;
}

uint32_t decodeCivFrequencyBytes(const uint8_t *bytes, size_t byteCount){
  uint32_t value = 0;
  for (size_t i = 0; i < byteCount; i++) {
    size_t src = byteCount - 1 - i;
    value += (bytes[src] >> 4) * decMulti[i * 2];
    value += (bytes[src] & 0x0F) * decMulti[i * 2 + 1];
  }
  return value;
}

uint32_t decodeCivBcdBytes(const uint8_t *bytes, size_t byteCount){
  uint32_t value = 0;
  for (size_t i = 0; i < byteCount; i++) {
    value = value * 100 + ((bytes[i] >> 4) * 10) + (bytes[i] & 0x0F);
  }
  return value;
}

// LSB-first variant used for RIT (bytes[0] = least significant pair)
uint32_t decodeCivBcdBytesLsb(const uint8_t *bytes, size_t byteCount){
  uint32_t value = 0;
  uint32_t mult = 1;
  for (size_t i = 0; i < byteCount; i++) {
    value += (((bytes[i] >> 4) * 10) + (bytes[i] & 0x0F)) * mult;
    mult *= 100;
  }
  return value;
}

String decodeModeName(uint8_t modeId){
  switch (modeId) {
    case 0x00: return "LSB";
    case 0x01: return "USB";
    case 0x02: return "AM";
    case 0x03: return "CW";
    case 0x04: return "RTTY";
    case 0x05: return "FM";
    case 0x06: return "WFM";
    case 0x07: return "CW-R";
    case 0x08: return "RTTY-R";
    case 0x17: return "DV";
    default: return "UNK";
  }
}

String decodeFilterName(uint8_t filterId){
  switch (filterId) {
    case 0x01: return "FIL1";
    case 0x02: return "FIL2";
    case 0x03: return "FIL3";
    default: return "UNK";
  }
}


String extractJsonString(const String &json, const char *key){
  String token = "\"" + String(key) + "\":";
  int start = json.indexOf(token);
  if (start < 0) {
    return String();
  }
  start += token.length();
  while (start < (int)json.length() && (json.charAt(start) == ' ' || json.charAt(start) == '\t')) {
    start++;
  }
  if (start >= (int)json.length()) {
    return String();
  }

  if (json.charAt(start) == '"') {
    start++;
    String out;
    bool escaped = false;
    for (int i = start; i < (int)json.length(); i++) {
      char c = json.charAt(i);
      if (escaped) {
        switch (c) {
          case 'n':  out += '\n'; break;
          case 'r':  out += '\r'; break;
          case 't':  out += '\t'; break;
          case '\\': out += '\\'; break;
          case '"':  out += '"';  break;
          case 'u':  {
            // \uXXXX — decode 4 hex digits to char (BMP only, basic ASCII range)
            if (i + 4 < (int)json.length()) {
              char h[5] = { json.charAt(i+1), json.charAt(i+2), json.charAt(i+3), json.charAt(i+4), '\0' };
              unsigned int cp = (unsigned int)strtoul(h, nullptr, 16);
              if (cp < 0x80) out += (char)cp;
              i += 4;
            }
            break;
          }
          default:   out += c;    break;
        }
        escaped = false;
      } else if (c == '\\') {
        escaped = true;
      } else if (c == '"') {
        return out;
      } else {
        out += c;
      }
    }
    return String();
  }

  int end = start;
  while (end < (int)json.length() && json.charAt(end) != ',' && json.charAt(end) != '}') {
    end++;
  }
  String out = json.substring(start, end);
  out.trim();
  return out;
}

bool extractJsonBool(const String &json, const char *key, bool defaultValue){
  String value = extractJsonString(json, key);
  if (value.length() == 0) {
    return defaultValue;
  }
  value.toLowerCase();
  if (value == "true" || value == "1") {
    return true;
  }
  if (value == "false" || value == "0") {
    return false;
  }
  return defaultValue;
}

static String readLogConfigJson() {
  if (!LittleFS.exists(LOG_CONFIG_PATH)) {
    return String();
  }
  File f = LittleFS.open(LOG_CONFIG_PATH, "r");
  if (!f) {
    return String();
  }
  String json = f.readString();
  f.close();
  json.trim();
  return json;
}

static String buildLogConfigJson(
  const String &existingJson,
  const String &trx1Label,
  const String &trx2Label,
  const String &trx3Label,
  const String &rstSsb,
  const String &rstCwRtty,
  bool manualModeForPhone,
  const String &blockedDxcc
) {
  String json;
  json.reserve(256);
  json += "{";
  json += "\"trx1Label\":\""; json += jsonEscape(trx1Label); json += "\"";
  json += ",\"trx2Label\":\""; json += jsonEscape(trx2Label); json += "\"";
  json += ",\"trx3Label\":\""; json += jsonEscape(trx3Label); json += "\"";
  json += ",\"rstSsb\":\"";    json += jsonEscape(rstSsb);    json += "\"";
  json += ",\"rstCwRtty\":\""; json += jsonEscape(rstCwRtty); json += "\"";
  json += ",\"manualModeForPhone\":"; json += manualModeForPhone ? "true" : "false";
  json += ",\"blockedDxcc\":\""; json += jsonEscape(blockedDxcc); json += "\"";
  json += "}";
  return json;
}

static bool saveLogConfigJson(const String &json) {
  File f = LittleFS.open(LOG_CONFIG_PATH, "w");
  if (!f) {
    return false;
  }
  f.print(json);
  f.close();
  loadLogConfigVars();
  return true;
}

String extractJsonObject(const String &json, const char *key) {
  String token = "\"" + String(key) + "\":";
  int start = json.indexOf(token);
  if (start < 0) return String();
  start += token.length();
  while (start < (int)json.length() && (json[start] == ' ' || json[start] == '\t')) start++;
  if (start >= (int)json.length() || json[start] != '{') return String();
  int depth = 0, end = start;
  bool inString = false;
  bool escaped = false;
  for (; end < (int)json.length(); end++) {
    char c = json[end];
    if (inString) {
      if (escaped) escaped = false;
      else if (c == '\\') escaped = true;
      else if (c == '"') inString = false;
      continue;
    }
    if (c == '"') inString = true;
    else if (c == '{') depth++;
    else if (c == '}') { if (--depth == 0) { end++; break; } }
  }
  return json.substring(start, end);
}

int extractJsonInt(const String &j, const String &key) {
  String needle = "\"" + key + "\":";
  int idx = j.indexOf(needle);
  if (idx < 0) return 0;
  return j.substring(idx + needle.length()).toInt();
}

void bdLoadDefaults() {
  const uint32_t fMin[BD_ROWS] = {
    1810, 3500, 5351, 7000, 10100, 14000, 18068,
    21000, 24890, 28000, 50000, 70000, 144000, 430000, 0, 0
  };
  const uint32_t fMax[BD_ROWS] = {
    2000, 3800, 5367, 7200, 10150, 14350, 18168,
    21450, 24990, 29700, 54000, 70500, 146000, 440000, 0, 0
  };
  for (int i = 0; i < BD_ROWS; i++) {
    bdRows[i].fMin    = fMin[i];
    bdRows[i].fMax    = fMax[i];
    bdRows[i].outputs = (i < 14) ? (uint16_t)(1 << i) : 0;
  }
  bdSource = 1;
}

void bdLoadConfig() {
  if (!LittleFS.exists(BD_CONFIG_PATH)) { bdLoadDefaults(); return; }
  File f = LittleFS.open(BD_CONFIG_PATH, FILE_READ);
  if (!f) { bdLoadDefaults(); return; }
  String j = f.readString();
  f.close();
  int si = j.indexOf("\"source\":");
  if (si >= 0) bdSource = j.substring(si + 9).toInt();
  int arrStart = j.indexOf("\"rows\":[");
  if (arrStart < 0) { bdLoadDefaults(); return; }
  arrStart += 8;
  for (int i = 0; i < BD_ROWS; i++) {
    int ob = j.indexOf('{', arrStart);
    int cb = j.indexOf('}', ob);
    if (ob < 0 || cb < 0) break;
    String row = j.substring(ob, cb + 1);
    bdRows[i].fMin    = (uint32_t)extractJsonInt(row, "fMin");
    bdRows[i].fMax    = (uint32_t)extractJsonInt(row, "fMax");
    bdRows[i].outputs = (uint16_t)extractJsonInt(row, "outputs");
    arrStart = cb + 1;
  }
}

void bdSaveConfig() {
  File f = LittleFS.open(BD_CONFIG_PATH, "w");
  if (!f) return;
  f.print("{\"source\":"); f.print(bdSource);
  f.print(",\"rows\":[");
  for (int i = 0; i < BD_ROWS; i++) {
    if (i > 0) f.print(",");
    f.print("{\"fMin\":"); f.print(bdRows[i].fMin);
    f.print(",\"fMax\":"); f.print(bdRows[i].fMax);
    f.print(",\"outputs\":"); f.print(bdRows[i].outputs);
    f.print("}");
  }
  f.print("]}");
  f.close();
}

void bdWriteOutputs(uint16_t mask) {
  uint8_t hi = (mask >> 8) & 0xFF;
  uint8_t lo = mask & 0xFF;
  digitalWrite(BD_LATCH_PIN, LOW);
  shiftOut(BD_DATA_PIN, BD_CLOCK_PIN, MSBFIRST, hi);
  shiftOut(BD_DATA_PIN, BD_CLOCK_PIN, MSBFIRST, lo);
  digitalWrite(BD_LATCH_PIN, HIGH);
  bdCurrentOutputs = mask;
}

void bdInit() {
  if (!bdEnabled) return;
  pinMode(BD_CLOCK_PIN, OUTPUT); digitalWrite(BD_CLOCK_PIN, LOW);
  pinMode(BD_LATCH_PIN, OUTPUT); digitalWrite(BD_LATCH_PIN, HIGH);
  pinMode(BD_DATA_PIN,  OUTPUT); digitalWrite(BD_DATA_PIN,  LOW);
  bdWriteOutputs(0);
}

void bdUpdate(uint32_t freqHz) {
  if (!bdEnabled) return;
  uint32_t freqKhz = freqHz / 1000;
  uint16_t mask = 0;
  for (int i = 0; i < BD_ROWS; i++) {
    if (bdRows[i].fMin == 0 && bdRows[i].fMax == 0) continue;
    if (freqKhz >= bdRows[i].fMin && freqKhz <= bdRows[i].fMax) {
      mask |= bdRows[i].outputs;
    }
  }
  if (mask != bdCurrentOutputs) bdWriteOutputs(mask);
}

bool parseHexPayload(const String &hex, uint8_t *buffer, size_t &bufferLen, size_t maxLen){
  bufferLen = 0;
  int nibble = -1;
  for (size_t i = 0; i < hex.length(); i++) {
    char c = hex.charAt(i);
    if (c == ' ' || c == '\t' || c == '\n' || c == '\r') {
      continue;
    }

    int value;
    if (c >= '0' && c <= '9') {
      value = c - '0';
    } else if (c >= 'a' && c <= 'f') {
      value = 10 + c - 'a';
    } else if (c >= 'A' && c <= 'F') {
      value = 10 + c - 'A';
    } else {
      return false;
    }

    if (nibble < 0) {
      nibble = value;
    } else {
      if (bufferLen >= maxLen) {
        return false;
      }
      buffer[bufferLen++] = (uint8_t)((nibble << 4) | value);
      nibble = -1;
    }
  }
  return nibble < 0 && bufferLen > 0;
}

void setModesText(const char *value){
  portENTER_CRITICAL(&stateMux);
  snprintf(modes, sizeof(modes), "%s", value != nullptr ? value : "");
  portEXIT_CRITICAL(&stateMux);
}

void copyModesText(char *dest, size_t destSize){
  if (dest == nullptr || destSize == 0) {
    return;
  }

  portENTER_CRITICAL(&stateMux);
  snprintf(dest, destSize, "%s", modes);
  portEXIT_CRITICAL(&stateMux);
}

bool parseModeId(const String &modeName, uint8_t &modeId){
  String normalized = modeName;
  normalized.toUpperCase();
  if (normalized == "LSB") {
    modeId = MODE_TYPE_LSB;
    return true;
  }
  if (normalized == "USB") {
    modeId = MODE_TYPE_USB;
    return true;
  }
  if (normalized == "AM") {
    modeId = MODE_TYPE_AM;
    return true;
  }
  if (normalized == "CW") {
    modeId = MODE_TYPE_CW;
    return true;
  }
  if (normalized == "RTTY" || normalized == "FSK") {
    modeId = MODE_TYPE_RTTY;
    return true;
  }
  if (normalized == "FM") {
    modeId = MODE_TYPE_FM;
    return true;
  }
  if (normalized == "DV") {
    modeId = MODE_TYPE_DV;
    return true;
  }
  return false;
}

uint8_t parseFilterWidth(const String &filterName){
  String normalized = filterName;
  normalized.toUpperCase();
  if (normalized == "FIL2" || normalized == "MID" || normalized == "MEDIUM") {
    return IF_PASSBAND_WIDTH_MEDIUM;
  }
  if (normalized == "FIL3" || normalized == "NAR" || normalized == "NARROW") {
    return IF_PASSBAND_WIDTH_NARROW;
  }
  return IF_PASSBAND_WIDTH_WIDE;
}

size_t buildSimpleCatFrame(uint8_t command, const uint8_t *payload, size_t payloadLen, uint8_t *frame, size_t frameMaxLen){
  if (radio_address == 0x00 || frameMaxLen < payloadLen + 6) {
    return 0;
  }

  size_t frameLen = 0;
  frame[frameLen++] = START_BYTE;
  frame[frameLen++] = START_BYTE;
  frame[frameLen++] = radio_address;
  frame[frameLen++] = CONTROLLER_ADDRESS;
  frame[frameLen++] = command;
  for (size_t i = 0; i < payloadLen; i++) {
    frame[frameLen++] = payload[i];
  }
  frame[frameLen++] = STOP_BYTE;
  return frameLen;
}

size_t buildSetFrequencyFrame(uint32_t freqHz, uint8_t *frame, size_t frameMaxLen){
  String strFreq = IntToTenString(freqHz);
  String splitFreq[5];
  SplitString(strFreq, splitFreq);

  uint8_t payload[5] = {
    stringToByte(splitFreq[4]),
    stringToByte(splitFreq[3]),
    stringToByte(splitFreq[2]),
    stringToByte(splitFreq[1]),
    stringToByte(splitFreq[0])
  };
  return buildSimpleCatFrame(CMD_WRITE_FREQ, payload, sizeof(payload), frame, frameMaxLen);
}

size_t buildSetModeFrame(uint8_t modeId, uint8_t modeWidth, uint8_t *frame, size_t frameMaxLen){
  uint8_t payload[2] = {modeId, modeWidth};
  return buildSimpleCatFrame(CMD_WRITE_MODE, payload, sizeof(payload), frame, frameMaxLen);
}

size_t buildReadQuickSplitFrame(uint8_t *frame, size_t frameMaxLen){
  uint8_t payload[3] = {0x05, 0x00, 0x45};
  return buildSimpleCatFrame(0x1A, payload, sizeof(payload), frame, frameMaxLen);
}

void resetSetupMessages(void){
  setupSsidErr = "";
  setupPswdErr = "";
  setupSsid2Err = "";
  setupPswd2Err = "";
  setupCivAddrErr = "";
  setupSaveOk = false;
}

String setupTemplateProcessor(const String &key){
  if (key == "APMODE_TEXT") return APmode ? "AP mode ON" : "AP mode OFF";
  if (key == "MAC") return MACString;
  if (key == "REV") return String(REV);
  if (key == "HWREV") return String(HardwareRev);
  if (key == "SSID") return SSID;
  if (key == "PSWD") return PSWD;
  if (key == "SSID2") return SSID2;
  if (key == "PSWD2") return PSWD2;
  if (key == "TRXNET_PORT") return String(TRXNET_PORT);
  if (key == "TRXNET_ID") { char h[3]; snprintf(h, sizeof(h), "%02x", TRXNET_ID); return String(h); }
  if (key == "TRX2_NET_ID") { char h[3]; snprintf(h, sizeof(h), "%02x", TRX2_NET_ID); return String(h); }
  if (key == "TRX3_NET_ID") { char h[3]; snprintf(h, sizeof(h), "%02x", TRX3_NET_ID); return String(h); }
  if (key == "TRXNET_DEVICE_NAME") return TRXNET_ID != 0x00 ? String(trxDeviceName) : String("disabled");
  if (key == "TRXNET_AP_NOTE") return APmode
    ? "<span class=\"ap-note\">TrxNet is not active in AP mode — requires WiFi station mode.</span>"
    : "";
  if (key == "TRX1_LABEL") return g_lcTrx1Label;
  if (key == "TRX2_LABEL") return g_lcTrx2Label;
  if (key == "TRX3_LABEL") return g_lcTrx3Label;
  if (key == "RST_SSB") return g_lcRstSsb;
  if (key == "RST_CW_RTTY") return g_lcRstCwRtty;
  if (key == "MANUAL_MODE_FOR_PHONE_CHK") return g_lcManualModeForPhone ? "checked" : "";
  if (key == "BLOCKED_DXCC") return g_lcBlockedDxcc;
  if (key == "SSID_ERR") return setupSsidErr;
  if (key == "PSWD_ERR") return setupPswdErr;
  if (key == "SSID2_ERR") return setupSsid2Err;
  if (key == "PSWD2_ERR") return setupPswd2Err;
  if (key == "CIV_ADDR") {
    String addr = String(configuredCivAddress, HEX);
    addr.toUpperCase();
    if (configuredCivAddress < 16) {
      addr = "0" + addr;
    }
    return addr;
  }
  if (key == "CIV_ADDR_ERR") return setupCivAddrErr;
  if (key == "TRX_IC705_SEL") return transceiverType == "IC-705-BT" ? "selected" : "";
  if (key == "TRX_IC7610_SEL") return transceiverType == "IC-7610-CI-V" ? "selected" : "";
  if (key == "CW_MEM1") return cwMemoryText[0];
  if (key == "CW_MEM2") return cwMemoryText[1];
  if (key == "CW_MEM3") return cwMemoryText[2];
  if (key == "CW_MEM4") return cwMemoryText[3];
  if (key == "FREQ_MEM1") return freqMemoryText[0];
  if (key == "FREQ_MEM2") return freqMemoryText[1];
  if (key == "FREQ_MEM3") return freqMemoryText[2];
  if (key == "FREQ_MEM4") return freqMemoryText[3];
  if (key == "FREQ_MEM5") return freqMemoryText[4];
  if (key == "FREQ_MEM6") return freqMemoryText[5];
  if (key == "FREQ_MEM7") return freqMemoryText[6];
  if (key == "FREQ_MEM8") return freqMemoryText[7];
  if (key == "FREQ_MEM9") return freqMemoryText[8];
  if (key == "FREQ_MEM10") return freqMemoryText[9];
  if (key == "BAUD1200_SEL") return BaudRate == 1200 ? "selected" : "";
  if (key == "BAUD2400_SEL") return BaudRate == 2400 ? "selected" : "";
  if (key == "BAUD4800_SEL") return BaudRate == 4800 ? "selected" : "";
  if (key == "BAUD9600_SEL") return BaudRate == 9600 ? "selected" : "";
  if (key == "BAUD115200_SEL") return BaudRate == 115200 ? "selected" : "";
  if (key == "CW_IP_CHK") return cwIpOnConnect ? "checked" : "";
  if (key == "DXC_HOST") return DxcHost;
  if (key == "DXC_PORT") return DxcPort > 0 ? String(DxcPort) : "";
  if (key == "DXC_CALL") return DxcCallsign;
  if (key == "DXC_LOCATOR") return DxcLocator;
  if (key == "BT_NAME") return BT_NAME;
  return String();
}

bool sendTemplatedHtml(const char *path){
  webQuietUntil = millis() + 1500;
  webServer.sendHeader("Connection", "close");
  webServer.client().setNoDelay(true);
  if (!LittleFS.exists(path)) {
    String msg = "Missing ";
    msg += path;
    msg += " in LittleFS";
    webServer.send(500, "text/plain", msg);
    return false;
  }
  File file = LittleFS.open(path, "r");
  if (!file) {
    webServer.send(500, "text/plain", "File open failed");
    return false;
  }

  String page;
  page.reserve(file.size() + 1024);
  String line;
  line.reserve(256);
  file.setTimeout(10);

  while (file.available()) {
    #if defined(WDT)
      esp_task_wdt_reset();
    #endif
    line = file.readStringUntil('\n');
    int start = 0;
    while (true) {
      int p1 = line.indexOf('%', start);
      if (p1 < 0) { page += line.substring(start); break; }
      int p2 = line.indexOf('%', p1 + 1);
      if (p2 < 0) { page += line.substring(start); break; }
      page += line.substring(start, p1);
      page += setupTemplateProcessor(line.substring(p1 + 1, p2));
      start = p2 + 1;
    }
    if (file.available()) page += '\n';
  }
  file.close();

  webServer.sendHeader("Cache-Control", "no-cache, no-store, must-revalidate");
  webServer.sendHeader("Pragma", "no-cache");
  webServer.sendHeader("Connection", "close");
  webServer.client().setNoDelay(true);
  webServer.setContentLength(page.length());
  webServer.send(200, "text/html", page);
  webQuietUntil = millis() + 1500;
  return true;
}

void renderSetupPage(){
  handleFileFromSPIFFS("/setup.html");
}

void handleSetupData(){
  char trxnetHex[3];
  snprintf(trxnetHex, sizeof(trxnetHex), "%02x", TRXNET_ID);

  int baudSelect = 3;
  if (BaudRate == 1200) baudSelect = 0;
  else if (BaudRate == 2400) baudSelect = 1;
  else if (BaudRate == 4800) baudSelect = 2;
  else if (BaudRate == 9600) baudSelect = 3;
  else if (BaudRate == 115200) baudSelect = 4;

  uint8_t ipLastOctet = APmode ? 0 : (uint8_t)WiFi.localIP()[3];
  bool trxnetidIsDefault = (EEPROM.read(41) == 0xff);

  String j;
  j.reserve(3500);
  j += "{\"fwRev\":"; j += (unsigned)REV;
  j += ",\"apMode\":"; j += APmode ? "true" : "false";
  j += ",\"apModeText\":\""; j += APmode ? "AP mode ON" : "AP mode OFF"; j += "\"";
  j += ",\"mac\":\""; j += configJsonEscape(MACString); j += "\"";
  j += ",\"hwRev\":"; j += HardwareRev;
  j += ",\"ipLastOctet\":"; j += ipLastOctet;
  j += ",\"hostname\":\""; j += deviceHostname; j += "\"";
  // Address the router last handed out. In AP mode this is the only clue the
  // portal can offer about where the device lives on the real network.
  j += ",\"lastStaIp\":\"";
  j += ((uint32_t)lastStaIp != 0) ? lastStaIp.toString() : String("");
  j += "\"";
  j += ",\"trxnetidIsDefault\":"; j += trxnetidIsDefault ? "true" : "false";
  j += ",\"trxnetDeviceName\":\""; j += configJsonEscape(TRXNET_ID != 0x00 ? String(trxDeviceName) : String("disabled")); j += "\"";
  j += ",\"trxnetApNote\":\""; j += APmode ? "TrxNet is not active in AP mode - requires WiFi station mode." : ""; j += "\"";
  j += ",\"ssid\":\""; j += configJsonEscape(SSID); j += "\"";
  j += ",\"pswd\":\""; j += configJsonEscape(PSWD); j += "\"";
  j += ",\"ssid2\":\""; j += configJsonEscape(SSID2); j += "\"";
  j += ",\"pswd2\":\""; j += configJsonEscape(PSWD2); j += "\"";
  j += ",\"trxnetid\":\""; j += trxnetHex; j += "\"";
  j += ",\"trxnetport\":\""; j += TRXNET_PORT; j += "\"";
  j += ",\"trxnetprio\":\""; j += configJsonEscape(TRXNET_PRIO); j += "\"";
  j += ",\"baud\":\""; j += baudSelect; j += "\"";
  String labels[3] = {g_lcTrx1Label, g_lcTrx2Label, g_lcTrx3Label};
  for (uint8_t slot = 0; slot < 3; slot++) {
    char civ[3], netid[3];
    snprintf(civ, sizeof(civ), "%02X", radioSlots[slot].civAddr);
    snprintf(netid, sizeof(netid), "%02X", radioSlots[slot].netId);
    String prefix = "trx" + String(slot + 1);
    j += ",\""; j += prefix; j += "enabled\":";
    j += (slot == 0 || radioSlots[slot].enabled) ? "true" : "false";
    j += ",\""; j += prefix; j += "label\":\"";
    j += configJsonEscape(labels[slot]); j += "\"";
    j += ",\""; j += prefix; j += "transport\":\"";
    j += radioTransportName(radioSlots[slot].transport); j += "\"";
    j += ",\""; j += prefix; j += "civaddr\":\""; j += civ; j += "\"";
    j += ",\""; j += prefix; j += "netid\":\""; j += netid; j += "\"";
    j += ",\""; j += prefix; j += "lanip\":\"";
    j += configJsonEscape(radioSlots[slot].lanIp); j += "\"";
    j += ",\""; j += prefix; j += "lanuser\":\"";
    j += configJsonEscape(radioSlots[slot].lanUser); j += "\"";
    j += ",\""; j += prefix; j += "lanpass\":\"";
    j += configJsonEscape(radioSlots[slot].lanPass); j += "\"";
    j += ",\""; j += prefix; j += "model\":\"";
    j += configJsonEscape(radioSlots[slot].model); j += "\"";
  }
  // Compatibility aliases used by the current JS8 readiness check and older
  // setup backups while the unified per-slot keys become authoritative.
  { char civ[3]; snprintf(civ, sizeof(civ), "%02X", radioSlots[0].civAddr);
    j += ",\"civaddr\":\""; j += civ; j += "\""; }
  j += ",\"lanip\":\"";   j += configJsonEscape(radioSlots[0].lanIp); j += "\"";
  j += ",\"lanuser\":\""; j += configJsonEscape(radioSlots[0].lanUser); j += "\"";
  j += ",\"lanpass\":\""; j += configJsonEscape(radioSlots[0].lanPass); j += "\"";
  j += ",\"cwIpOnConnect\":"; j += cwIpOnConnect ? "true" : "false";
  j += ",\"trx2conntype\":"; j += TRX2_CONN_TYPE;
  j += ",\"trx3conntype\":"; j += TRX3_CONN_TYPE;
  j += ",\"dxchost\":\""; j += configJsonEscape(DxcHost); j += "\"";
  j += ",\"dxcport\":\""; j += DxcPort > 0 ? String(DxcPort) : ""; j += "\"";
  j += ",\"dxccall\":\""; j += configJsonEscape(DxcCallsign); j += "\"";
  j += ",\"dxclocator\":\""; j += configJsonEscape(DxcLocator); j += "\"";
  j += ",\"rstSsb\":\""; j += configJsonEscape(g_lcRstSsb); j += "\"";
  j += ",\"rstCwRtty\":\""; j += configJsonEscape(g_lcRstCwRtty); j += "\"";
  j += ",\"manualModeForPhone\":"; j += g_lcManualModeForPhone ? "true" : "false";
  j += ",\"blockedDxcc\":\""; j += configJsonEscape(g_lcBlockedDxcc); j += "\"";
  for (uint8_t i = 0; i < CW_MEMORY_COUNT; i++) {
    j += ",\"cwmem"; j += (i + 1); j += "\":\""; j += configJsonEscape(cwMemoryText[i]); j += "\"";
  }
  for (uint8_t i = 0; i < FREQ_MEMORY_COUNT; i++) {
    j += ",\"freqmem"; j += (i + 1); j += "\":\""; j += configJsonEscape(freqMemoryText[i]); j += "\"";
  }
  j += "}";
  webServer.sendHeader("Cache-Control", "no-cache, no-store, must-revalidate");
  webServer.sendHeader("Pragma", "no-cache");
  webServer.sendHeader("Connection", "close");
  webServer.client().setNoDelay(true);
  webServer.send(200, "application/json", j);
}

// Live list of visible TrxNet devices (peer table) for the setup page.
// state: "ap" (AP mode) / "disabled" (NET_ID 0x00) / "ok". prio computed server-side.
void handleTrxNetPeers(){
  String j;
  j.reserve(1024);
  j += "{";
  if (APmode) {
    j += "\"state\":\"ap\",\"self\":\"\",\"peers\":[]";
  } else if (!trxNetEnabled) {
    j += "\"state\":\"disabled\",\"self\":\"\",\"peers\":[]";
  } else {
    j += "\"state\":\"ok\",\"self\":\""; j += configJsonEscape(String(trxDeviceName)); j += "\",\"peers\":[";
    uint32_t now = millis();
    int count = net.peerCount();
    bool first = true;
    for (int i = 0; i < count; i++) {
      const TrxPeer* p = net.peer(i);
      if (!p || !p->active) continue;
      if (!first) j += ",";
      first = false;
      uint32_t age = (now - p->lastSeen) / 1000;
      j += "{\"name\":\""; j += configJsonEscape(String(p->name)); j += "\"";
      j += ",\"ip\":\"";   j += p->ip.toString(); j += "\"";
      j += ",\"age\":";    j += age;
      j += ",\"prio\":";   j += trxIsPriorityName(p->name) ? "true" : "false";
      j += "}";
    }
    j += "]";
  }
  j += "}";
  webServer.sendHeader("Cache-Control", "no-cache, no-store, must-revalidate");
  webServer.sendHeader("Connection", "close");
  webServer.client().setNoDelay(true);
  webServer.send(200, "application/json", j);
}

// ---- LAN radio discovery endpoints (SETUP page) ----------------------------
// Shape follows the two existing precedents: /lan/reconnect for a fire-and-
// forget command that the main loop picks up, /trxnet-peers.json for a list the
// browser polls. Nothing long-running happens inside a handler.

static void icomScanSendJson(int code, const String &body) {
  webServer.sendHeader("Cache-Control", "no-cache, no-store, must-revalidate");
  webServer.sendHeader("Connection", "close");
  webServer.client().setNoDelay(true);
  webServer.send(code, "application/json", body);
}

// Refuses rather than queues: a scan borrows the radio link, so the operator
// should see why it did not run instead of it happening at some later moment.
static const char* icomScanRefusal() {
  if (APmode) return "ap";
  if (WiFi.status() != WL_CONNECTED) return "no_wifi";
  if (icomScanPhase != ISCAN_IDLE && icomScanPhase != ISCAN_DONE) return "busy";
  if (txRealtimeNow()) return "tx";
  return nullptr;
}

void handleIcomScanStart(){
  const char* refusal = icomScanRefusal();
  if (refusal) {
    icomScanSendJson(409, String("{\"ok\":false,\"error\":\"") + refusal + "\"}");
    return;
  }
  icomScanFailed = false;
  icomScanPhase = ISCAN_SUSPEND;
  icomScanSendJson(202, "{\"ok\":true}");
}
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
void loop(){
  static bool serialFlushed = false;
  if (!serialFlushed && millis() > 2000) {
    while (Serial.available()) Serial.read();
    serialFlushed = true;
  }
  #define _TIMED(name, call) { unsigned long _t = millis(); call; unsigned long _d = millis()-_t; if(_d > LOOP_WARN_MS) { Serial.print("LOOP| slow: " name " "); Serial.print(_d); Serial.println("ms"); } }
  _TIMED("Watchdog",        Watchdog())
  _TIMED("LanClient",       lanClientLoop())
  audioPttSafetyRetryTick();
  // PTT release is checked immediately after the two radio Interfaces. The
  // dedicated audio owner advances playout independently; this early check
  // prevents unrelated CLI/web work from extending the keyed tail.
  if(aud1TxState == AUD1_TX_STREAM) aud1TxTick(false);
  _TIMED("CLI",             serialPump())
  _TIMED("CIV",             civPollTick())
  #if defined(RTLE)
    _TIMED("rtleserver",    rtleserver.handleClient())
  #endif
  handleWebServerLoop();
  _TIMED("NetIdentity",     NetworkIdentityLoop())
  _TIMED("RadioModel",      radioModelLearnTick())
  _TIMED("WifiTry",         wifiTryTick())
  _TIMED("IcomScan",        icomScanTick())
  _TIMED("TrxNet",          TrxNetLoop())
  _TIMED("DxcLoop",         DxcLoop())
  _TIMED("dxcRaw",          dxcHandleRawClient())
  _TIMED("audioRaw",        audioHandleRawClient())
  _TIMED("audioWs",         AudioHandleWsClient())
  // Persist queued unattended-log events to flash only when no slot key is near,
  // so the append/rotate never stalls the loop across a JS8 slot boundary.
  if(!txRealtimeNow()) unattendedLogFlush();

  // TrxNet: process pending /s-hz command (set TRX1 VFO via CI-V)
  if (trxFreqPending) {
    trxFreqPending = false;
    uint32_t f = trxPendingHz;
    if (f > 0) {
      if (radioSetFrequency(f)) {
        if (Debug) Serial.printf("CAT | set VFO %lu\n", (unsigned long)f);
      } else {
        if (Debug) Serial.println("CAT | set VFO skipped, TRX not connected");
      }
    }
  }

  statusFlashTick();

  // AP mode: status LED fade in/out
  if(APmode==true){
    static int PwmValue = 0;
    static bool PwmDir = true;
    static long pwmTimer = 0;
    if(millis()-pwmTimer>3){
      if(PwmDir==true){
        PwmValue++;
        if(PwmValue>254){ PwmDir=false; }
      }else{
        PwmValue--;
        if(PwmValue<1){ PwmDir=true; }
      }
      ledcWrite(pwmChannel, PwmValue);
      pwmTimer=millis();
    }
  }
}

// SUBROUTINES -------------------------------------------------------------------------------------------------------

void handleBtEvents(){
  if (btStateBroadcastPending == true) {
    btStateBroadcastPending = false;
  }

  if (btConnectPending == true) {
    btConnectPending = false;
    btClientConnected = true;
    radio_address = configuredCivAddress;
    frequency = 0;
    frequencyTmp = 0;
    if (TrxSetupDone == false) {
      TrxNeedSet = 1;
      if (cwIpOnConnect) cwIpSendPending = true;
    }
    Serial.println("    | Client Connected");
  }

  if (btDisconnectPending == true) {
    btDisconnectPending = false;
    btClientConnected = false;
    radio_address = 0x00;
    TrxNeedSet = 0;
    powerTimer = 0;
    frequency = 0;
    frequencyTmp = 0;
    setModesText("OFF");
    Serial.println("    | Client Disconnected");
    if (statusPower == 1 && trxNetEnabled) {
      uint32_t zero = 0;
      net.publish("/hz", (uint8_t*)&zero, sizeof(zero));
    }
  }
}

// CW IP announcement: values applied during the announce and restored afterward.
static const uint8_t       CW_ANNOUNCE_AF_GAIN = 102;    // ~40% of 255, audible without blasting
static const unsigned long CW_ANNOUNCE_KEY_MS  = 12000;  // max time to let the keyer finish

// Encode a 0..255 level into the IC-705's 2-byte BCD level format (e.g. 255 -> 02 55).
static inline void encodeCivLevel(uint16_t value, uint8_t out[2]){
  if (value > 255) value = 255;
  out[0] = (uint8_t)(value / 100);                              // hundreds (0..2)
  out[1] = (uint8_t)((((value / 10) % 10) << 4) | (value % 10));// tens|units BCD
}

// Blocking wait that keeps the active transport, web and TrxNet serviced. Unlike
// ServiceBackgroundTasks it also pumps lanClient, so a multi-second CW keying wait
// doesn't starve the LAN control channel (which would drop the radio session).
static void cwAnnounceService(unsigned long ms){
  unsigned long start = millis();
  while (millis() - start < ms) {
    if (radioSlots[0].transport == RADIO_LAN) lanClient.loop();
    else if (radioSlots[0].transport == RADIO_CIV) {
      serialPump();
      civPollTick();
    }
    secondaryLanClientsLoop();
    if (trxNetEnabled) net.loop();
    if (APmode) dnsServer.processNextRequest();
    webServer.handleClient();
    #if defined(WDT)
      esp_task_wdt_reset();
    #endif
    delay(5);
  }
}

// Announce the interface's WiFi IP in CW on the radio, as sidetone only: BK-IN is
// forced OFF so the keyer never keys the transmitter — nothing goes on air and no
// interference is caused. RF gain is dropped to minimum so band noise doesn't mask
// the tone. Transport-agnostic: works over BT and LAN because catWriteFrame()
// routes to whichever link is up. Snapshots every setting it touches (mode+filter+
// DATA, BK-IN, AF gain, RF gain) up front and restores them all when finished.
void announceIpViaCw(){
  if (radio_address == 0x00) return;
  uint8_t frame[16];
  size_t  n;

  // 1. Read back the settings we're about to change, so we can restore them.
  { uint8_t p[] = {0x00}; n = buildSimpleCatFrame(0x26, p, sizeof(p), frame, sizeof(frame)); catWriteFrame(frame, n, false); } // mode+data+filter
  { uint8_t p[] = {0x01}; n = buildSimpleCatFrame(0x14, p, sizeof(p), frame, sizeof(frame)); catWriteFrame(frame, n, false); } // AF gain
  { uint8_t p[] = {0x02}; n = buildSimpleCatFrame(0x14, p, sizeof(p), frame, sizeof(frame)); catWriteFrame(frame, n, false); } // RF gain
  { uint8_t p[] = {0x47}; n = buildSimpleCatFrame(0x16, p, sizeof(p), frame, sizeof(frame)); catWriteFrame(frame, n, false); } // BK-IN
  cwAnnounceService(700); // let the replies land in the state globals

  const uint8_t savedModeId = stateModeId;
  const bool    savedData   = stateDataMode;
  const uint8_t savedFilter = stateFilter;
  const uint8_t savedAf     = stateAfGain;
  const uint8_t savedRf     = stateRfGain;
  const uint8_t savedBk     = stateVoxMode;
  Serial.printf(" CW | announce IP, saved mode=0x%02X data=%d fil=%u af=%u rf=%u bk=%u\n",
                (unsigned)savedModeId, (int)savedData, (unsigned)savedFilter,
                (unsigned)savedAf, (unsigned)savedRf, (unsigned)savedBk);

  // 2. Set up a sidetone-only announcement: CW/FIL3, BK-IN OFF so the keyer never
  //    keys the transmitter (nothing goes on air, no interference), RF gain to
  //    minimum so band noise is muted, AF up so the sidetone is clearly audible.
  { uint8_t p[] = {0x00, 0x03, 0x00, 0x03}; n = buildSimpleCatFrame(0x26, p, sizeof(p), frame, sizeof(frame)); catWriteFrame(frame, n, false); } // CW, non-data, FIL3
  { uint8_t lv[2]; encodeCivLevel(CW_ANNOUNCE_AF_GAIN, lv); uint8_t p[] = {0x01, lv[0], lv[1]}; n = buildSimpleCatFrame(0x14, p, sizeof(p), frame, sizeof(frame)); catWriteFrame(frame, n, false); } // AF ~40%
  { uint8_t lv[2]; encodeCivLevel(0, lv);                   uint8_t p[] = {0x02, lv[0], lv[1]}; n = buildSimpleCatFrame(0x14, p, sizeof(p), frame, sizeof(frame)); catWriteFrame(frame, n, false); } // RF gain min -> mute band noise
  { uint8_t p[] = {0x47, 0x00}; n = buildSimpleCatFrame(0x16, p, sizeof(p), frame, sizeof(frame)); catWriteFrame(frame, n, false); } // BK-IN OFF -> never transmits
  cwAnnounceService(300);

  // 3. Play the IP (sidetone only — BK-IN is off, so this never goes on air).
  String ipStr = "IP " + WiFi.localIP().toString();
  ipStr.toCharArray(CwMsg, sizeof(CwMsg));
  setModesText("CW"); // sendCW() routes CAT-CW only when the mode text is "CW"
  sendCW();
  cwAnnounceService(CW_ANNOUNCE_KEY_MS); // wait for the keyer to finish before touching the radio again

  // 4. Restore everything, in reverse order. saved==0 means the snapshot read never
  //    landed (LAN doesn't poll these), so fall back rather than leaving the forced
  //    announce level in place permanently:
  //      RF -> max, because we forced it to 0 and leaving it there deafens the RX
  //            (nobody operates at RF gain 0, so 0 really does mean "read failed")
  //      AF -> keep the audible level, because writing 0 back would mute the radio
  //    BK-IN needs no fallback: default 0 == OFF == what we just set, so a missed
  //    read simply leaves TX disabled, which is the safe direction.
  { uint8_t p[] = {0x47, savedBk}; n = buildSimpleCatFrame(0x16, p, sizeof(p), frame, sizeof(frame)); catWriteFrame(frame, n, false); } // BK-IN
  { uint8_t lv[2]; encodeCivLevel(savedRf > 0 ? savedRf : 255, lv); uint8_t p[] = {0x02, lv[0], lv[1]}; n = buildSimpleCatFrame(0x14, p, sizeof(p), frame, sizeof(frame)); catWriteFrame(frame, n, false); } // RF gain
  if (savedAf > 0) { uint8_t lv[2]; encodeCivLevel(savedAf, lv); uint8_t p[] = {0x01, lv[0], lv[1]}; n = buildSimpleCatFrame(0x14, p, sizeof(p), frame, sizeof(frame)); catWriteFrame(frame, n, false); } // AF gain
  { uint8_t p[] = {0x00, savedModeId, (uint8_t)(savedData ? 0x01 : 0x00), savedFilter}; n = buildSimpleCatFrame(0x26, p, sizeof(p), frame, sizeof(frame)); catWriteFrame(frame, n, false); } // mode+data+filter
  cwAnnounceService(300);
  applyModeState(savedModeId, savedData); // restore local display/state immediately
  stateFilter = savedFilter;
  Serial.println(" CW | announce IP done, settings restored");
}

// BT CAT poll cadence. Every frame keeps the SPP link out of sniff mode and the
// coex arbiter then starves WiFi (TCP stalls → AP drops us), so idle cadence is
// slow. The CAT page requests /state?fast=1, which holds the fast cadence while
// it stays open; the log page and everything else run on the slow one.
void pollRadio(){
  static unsigned long catPollTimer = 0;
  static unsigned long auxPollTimer = 0;
  static uint8_t auxPollIndex = 0;
  static uint8_t modePollDivider = 0;

  if (!btClientConnected) return;
  bool fastCat = (long)(catFastUntil - millis()) > 0;
  // During a WiFi outage every BT frame keeps the SPP link out of sniff mode and
  // re-association then never succeeds (even with ESP_COEX_PREFER_WIFI). Web and
  // TrxNet are unreachable anyway — keep only a slow freq poll for the band decoder.
  bool wifiOutage = false;
  #if defined(WIFI)
    wifiOutage = !APmode && (WifiDownSince != 0);
  #endif

  unsigned long freqInterval = wifiOutage ? CAT_POLL_OUTAGE_MS
                                          : (fastCat ? CAT_POLL_FAST_MS : CAT_POLL_MS);
  if (millis() - catPollTimer > freqInterval) {
    catPollTimer = millis();
    if (radio_address == 0x00) {
      if (Debug == true) Serial.println("CAT | searching radio...");
      searchRadio();
    } else {
      sendCatRequest(CMD_READ_FREQ);
      if (!wifiOutage && (fastCat || ++modePollDivider >= CAT_MODE_EVERY)) {
        modePollDivider = 0;
        sendCatRequest(CMD_READ_MODE);
      }
      processCatMessages();
    }
  }

  if (cwIpSendPending && radio_address != 0x00) {
    cwIpSendPending = false;
    TrxSetupDone = true;
    announceIpViaCw(); // snapshots mode/filter/BK-IN/AF/RF, keys the IP, restores them
  }

  if (!wifiOutage && radio_address != 0x00 && millis() - auxPollTimer > (fastCat ? AUX_POLL_FAST_MS : AUX_POLL_MS)) {
    auxPollTimer = millis();
    uint8_t frame[10];
    size_t frameLen = 0;
    switch (auxPollIndex % 10) {
      case 0: { uint8_t p[] = {stateTx ? (uint8_t)0x11 : (uint8_t)0x02}; frameLen = buildSimpleCatFrame(0x15, p, 1, frame, sizeof(frame)); break; } // TX=power, RX=S-meter
      case 1: { uint8_t p[] = {stateTx ? (uint8_t)0x12 : (uint8_t)0x15}; frameLen = buildSimpleCatFrame(0x15, p, 1, frame, sizeof(frame)); break; } // TX=SWR, RX=supply
      case 2: { uint8_t p[] = {0x01}; frameLen = buildSimpleCatFrame(0x14, p, 1, frame, sizeof(frame)); break; } // AF gain
      case 3: { uint8_t p[] = {0x0C}; frameLen = buildSimpleCatFrame(0x14, p, 1, frame, sizeof(frame)); break; } // key speed
      case 4: { uint8_t p[] = {0x0A}; frameLen = buildSimpleCatFrame(0x14, p, 1, frame, sizeof(frame)); break; } // RF power
      case 5: { uint8_t p[] = {0x00}; frameLen = buildSimpleCatFrame(0x1C, p, 1, frame, sizeof(frame)); break; } // TX state
      case 6: { uint8_t p[] = {0x00}; frameLen = buildSimpleCatFrame(0x21, p, 1, frame, sizeof(frame)); break; } // RIT offset (sub 0x00)
      case 7: {                        frameLen = buildSimpleCatFrame(0x11, nullptr, 0, frame, sizeof(frame)); break; } // ATT
      case 8: { uint8_t p[] = {0x02}; frameLen = buildSimpleCatFrame(0x16, p, 1, frame, sizeof(frame)); break; } // PREAMP
      case 9: { uint8_t p[] = {0x47}; frameLen = buildSimpleCatFrame(0x16, p, 1, frame, sizeof(frame)); break; } // VOX/BKIN
    }
    if (frameLen > 0) catWriteFrame(frame, frameLen, false);
    processCatMessages();
    auxPollIndex++;
  }
}

void Watchdog(){
  #if defined(BLUETOOTH)
    handleBtEvents();
    pollRadio();
  #endif

  static unsigned long mqttFreqTimer = 0;

  // Primary LAN owns PWR/audio in lanClientLoop(). Direct serial CI-V is also a
  // full primary connection; TrxNet is intentionally telemetry+tune only and
  // must never energise PWR-OUT or arm CAT/CW/PTT side effects.
  if (radioSlots[0].transport == RADIO_CIV) {
    bool connected = radioSlotConnected(0);
    if (!connected) {
      if (statusPower == 1) {
        statusPower = 0;
        digitalWrite(PowerOnPin, LOW);
        Serial.println(" PWR| OFF (CI-V)");
      }
    } else {
      if (statusPower == 0) {
        statusPower = 1;
        digitalWrite(PowerOnPin, HIGH);
        Serial.println(" PWR| ON (CI-V)");
        if (cwIpOnConnect) cwIpSendPending = true;
      }
      if (cwIpSendPending && radio_address != 0x00) {
        cwIpSendPending = false;
        announceIpViaCw();
      }
    }

    if (connected && radio_address != 0x00 && millis() - mqttFreqTimer > 2000
        && frequencyTmp != frequency) {
      if (trxNetEnabled) {
        uint32_t f = (uint32_t)frequency;
        net.publish("/hz", (uint8_t*)&f, sizeof(f));
      }
      frequencyTmp = frequency;
      mqttFreqTimer = millis();
      if (bdEnabled && bdSource == 1) bdUpdate(frequency);
    }
  } else if (radioSlots[0].transport == RADIO_TRXNET) {
    if (statusPower == 1) {
      digitalWrite(PowerOnPin, LOW);
      Serial.println(" PWR| OFF (TRXNET limited)");
      statusPower = 0;
    }
  }

  // WIFI status
  #if defined(WIFI)
    unsigned long currentMillis = millis();
    // if WiFi is down, try reconnecting every CHECK_WIFI_TIME seconds
    // if ((WiFi.status() != WL_CONNECTED) && (currentMillis - WifiTimer >=WifiReconnect)) {
    //   Serial.print(millis());
    //   Serial.println("cReconnecting...");
    //   WiFi.disconnect();
    //   WiFi.reconnect();
    //   WifiTimer = currentMillis;
    // }
    if (!APmode && (currentMillis - WifiTimer >= WifiReconnect)) {
      if (WiFiStationReady()) {
        WifiDownSince = 0;
        WifiHardResetDone = false;
        if (WifiCoexPreferred) {
          esp_coex_preference_set(ESP_COEX_PREFER_BALANCE);
          WifiCoexPreferred = false;
          Serial.print(millis());
          Serial.println(" WIFI| coex back to balance");
        }
        uint8_t *bssid = WiFi.BSSID();
        if (bssid && (!wifiLastBssidValid || memcmp(wifiLastBssid, bssid, 6) != 0
                      || wifiLastChannel != WiFi.channel())) {
          memcpy(wifiLastBssid, bssid, 6);
          wifiLastChannel = WiFi.channel();
          wifiLastSsid = WiFi.SSID();
          wifiLastBssidValid = true;
        }
        WifiTimer = currentMillis;
      } else {
        if (WifiDownSince == 0) WifiDownSince = currentMillis;
        unsigned long downFor = currentMillis - WifiDownSince;
        wl_status_t st = WiFi.status();

        // With the BT link up the coex arbiter starves WiFi so badly that
        // re-association never succeeds — tilt RF time to WiFi until we are back.
        if (!WifiCoexPreferred && btClientConnected) {
          esp_coex_preference_set(ESP_COEX_PREFER_WIFI);
          WifiCoexPreferred = true;
          Serial.print(millis());
          Serial.println(" WIFI| coex prefer WiFi (BT active)");
        }

        // status 255 = driver no longer initialized; only a reboot brings it back
        if ((downFor >= WIFI_RESTART_AFTER_MS || st == WL_NO_SHIELD) && !stateTx) {
          Serial.print(millis());
          Serial.println(" WIFI| unrecoverable, restarting ESP");
          delay(100);
          ESP.restart();
        }
        // Radio off/on at most once per outage, and never while the BT SPP link is
        // up — esp_wifi_stop() then times out ("wifi un-init") and repeating the
        // cycle kills the driver (rx buffer init errors, status=255).
        bool hardReset = false;
        if (downFor >= WIFI_HARD_RESET_AFTER_MS && !WifiHardResetDone) {
          WifiHardResetDone = true;
          hardReset = !btClientConnected;
        }

        if (st == WL_DISCONNECTED || st == WL_CONNECT_FAILED || st == WL_NO_SSID_AVAIL) {
          ActiveWifiProfile = NextWifiProfile(ActiveWifiProfile);
          WiFiRetryActiveProfile("status", hardReset);
        } else {
          WiFiRetryActiveProfile("no ip", hardReset);
        }
        WifiTimer = currentMillis;
      }
    }
  #endif

  // WDT
  #if defined(WDT)
    if(millis()-WdtTimer > 5000){
      esp_task_wdt_reset();
      WdtTimer=millis();
    }
  #endif

}

//-------------------------------------------------------------------------------------------------------
// LAN transport service loop. Non-blocking; drives lanClient and mirrors the
// decoded frequency/mode into the same globals the BT path fills, so the web UI,
// TrxNet publish and band decoder work unchanged. Auto-reconnects on failure.
void lanClientLoop(){
  // A scan or credential test owns UDP 50001 right now. Letting the retry logic
  // re-open it here would put two sockets on the same port (SO_REUSEADDR makes
  // that succeed) and the probe replies would go to the wrong one.
  if (icomScanSuspendLan) return;
  secondaryLanClientsLoop();
  if (radioSlots[0].transport != RADIO_LAN) return;
  if (lanReconnectRequested) {
    lanReconnectRequested = false;
    lanClient.stop();
    lanRetryAt = 0;
    lanBackoff = 3000;
    IPAddress rip;
    if (rip.fromString(lanRadioIp) && lanUser.length() > 0 && lanPass.length() > 0) {
      Serial.println("LAN | manual reconnect requested");
      lanClient.begin(rip, 50001, lanUser.c_str(), lanPass.c_str(), configuredCivAddress);
    } else {
      Serial.println("LAN | manual reconnect skipped, configuration incomplete");
    }
  }
  lanClient.loop();
  if (!lanClient.connected()) lanLinkWasUp = false;   // re-arm the safety un-key
  // Arming lapses by itself so a forgotten tab cannot transmit for weeks;
  // unattendedExpire() fires once so the log does not repeat every loop.
  if (unattendedExpire(unattendedGuard, millis()))
    unattendedLogEvent(UEV_EXPIRE, "arming window elapsed");

  if (lanClient.connected()) {
    // Edge, not level: the unconditional safety TX OFF fires once per link-up.
    if (!lanLinkWasUp) { lanLinkWasUp = true; audioPttSafetyOnLink(); }
    lanBackoff = 3000;   // healthy link resets the reconnect backoff
    // (re)start RX audio if the DATA page is open but the audio channel isn't up
    // yet — covers WS-connected-before-LAN and LAN-reconnect-while-page-open.
    if (AudioWsClient.connected() && !lanClient.rxAudioActive()) lanClient.startRxAudio();
    if (statusPower == 0) {
      statusPower = 1;
      digitalWrite(PowerOnPin, HIGH);
      Serial.println(" PWR| ON (LAN)");
      if (cwIpOnConnect) cwIpSendPending = true; // arm CW IP announce on first link-up
    }
    // Announce the IP once the radio address is known (learned from the first
    // decoded frame). Same feature/flag as the BT path; snapshots + restores state.
    if (cwIpSendPending && radio_address != 0x00) {
      cwIpSendPending = false;
      announceIpViaCw();
    }
    // frequency/mode/meters are written directly by lanCivFrameHandler (shared
    // parser). Here we only propagate a frequency change to TrxNet + band decoder.
    if (trxNetEnabled && frequency != 0 && (uint32_t)frequency != lanFreqTmp) {
      uint32_t f = (uint32_t)frequency;
      net.publish("/hz", (uint8_t*)&f, sizeof(f));
      lanFreqTmp = (uint32_t)frequency;
      if (bdEnabled && bdSource == 1) bdUpdate(frequency);
    }
  } else {
    if (statusPower == 1) {
      statusPower = 0;
      digitalWrite(PowerOnPin, LOW);
      Serial.println(" PWR| OFF (LAN)");
      frequency = 0; frequencyTmp = 0; lanFreqTmp = 0;
      setModesText("OFF");
    }
    // On failure: release the radio session IMMEDIATELY (single-session radio
    // must free the old one before we retry), then wait an escalating backoff
    // so we don't hammer a radio that still holds a zombie session.
    if (lanClient.failed()) {
      lanClient.stop();                 // sends disconnect/token-release -> state IDLE
      lanRetryAt = millis() + lanBackoff;
      Serial.print("LAN | reconnect in "); Serial.print(lanBackoff/1000); Serial.println("s");
      if (lanBackoff < 20000) lanBackoff *= 2;
    } else if (lanClient.status() == IcomLanClient::LAN_IDLE && lanRetryAt && millis() >= lanRetryAt) {
      lanRetryAt = 0;
      IPAddress rip;
      if (rip.fromString(lanRadioIp))
        lanClient.begin(rip, 50001, lanUser.c_str(), lanPass.c_str(), configuredCivAddress);
    }
  }
}

//-------------------------------------------------------------------------------------------------------
// Last address the router gave us, kept so a later visit to the AP portal can
// still answer "where is the device". A fresh EEPROM reads 0xff everywhere.
void loadLastStaIp() {
  uint8_t a = EEPROM.read(LAST_STA_IP_ADDR + 0), b = EEPROM.read(LAST_STA_IP_ADDR + 1);
  uint8_t c = EEPROM.read(LAST_STA_IP_ADDR + 2), d = EEPROM.read(LAST_STA_IP_ADDR + 3);
  if (a == 0xff && b == 0xff && c == 0xff && d == 0xff) { lastStaIp = IPAddress(); return; }
  lastStaIp = IPAddress(a, b, c, d);
}

// Written only when the address actually changed -- this runs on every boot and
// EEPROM emulation rewrites a whole flash sector per commit.
void saveLastStaIp(IPAddress ip) {
  if ((uint32_t)ip == 0 || ip == lastStaIp) return;
  for (uint8_t i = 0; i < 4; i++) EEPROM.write(LAST_STA_IP_ADDR + i, ip[i]);
  EEPROM.commit();
  lastStaIp = ip;
}

//-------------------------------------------------------------------------------------------------------
// Drives the station link raised by /setup/wifi-try while the softAP is still
// up: scan, then try every configured profile the scan saw, strongest first.
//
// Trying only the first configured profile was wrong -- an unreachable SSID 1
// made the handoff report failure while SSID 2 was sitting there working. The
// boot path alternates between profiles for exactly this reason.
//
// Both the scan and the association move the shared radio, so clients on the
// portal see brief drops and re-associate; the page treats a failed poll as
// "still connecting".
// Every configured profile, in order, with no scan behind it. Used when the
// scan could not run or saw nothing: a scan result is an optimisation, being
// unable to scan is no reason to refuse to try the credentials the operator
// just typed. Hidden SSIDs never show up in a scan either.
uint8_t fillBlindWifiCandidates(WifiScanPick out[2]) {
  uint8_t count = 0;
  for (byte p = 0; p < 2; p++) {
    if (!WifiProfileConfigured(p)) continue;
    out[count] = WifiScanPick();
    out[count].profile = p;
    count++;
  }
  return count;
}

void wifiTryBeginCandidate() {
  const WifiScanPick &pick = wifiTryCandidates[wifiTryCandidateIdx];
  wifiTrySsid = WifiProfileSSID(pick.profile);
  String pswd = WifiProfilePSWD(pick.profile);
  ApplyStaIdentity();
  if (pick.targeted) {
    // We just heard this AP, so there is no reason to make the driver sweep
    // every channel again. Never pass the all-zero BSSID of a blind candidate
    // here -- that would ask the driver for a station that cannot exist.
    WiFi.begin(wifiTrySsid.c_str(), pswd.c_str(), pick.channel, pick.bssid);
  } else {
    WiFi.begin(wifiTrySsid.c_str(), pswd.c_str());
  }
  wifiTryState = WTRY_CONNECTING;
  wifiTryDeadline = millis() + 20000;
  Serial.print("WIFI| AP handoff: trying ");
  Serial.print(wifiTrySsid);
  if (pick.targeted) {
    Serial.print(" ch");
    Serial.print(pick.channel);
    Serial.print(" ");
    Serial.print(pick.rssi);
    Serial.println(" dBm");
  } else {
    Serial.println(" (no scan hit, connecting blind)");
  }
}

void wifiTryFail(const char* reason) {
  wifiTryState = WTRY_FAILED;
  wifiTryReason = reason;
  WiFi.disconnect(false, false);
  WiFi.mode(WIFI_AP);              // drop back to a clean portal-only AP
  Serial.print("WIFI| AP handoff failed: ");
  Serial.println(reason);
}

void wifiTryTick() {
  if (wifiTryState == WTRY_SCAN) {
    // Give the STA interface a moment to come up after WIFI_AP_STA before
    // asking it to scan.
    if ((long)(millis() - wifiTryDeadline) < 0) return;

    // Blocking scan, the same call the boot path uses successfully. The async
    // form was tried first and returned WIFI_SCAN_FAILED immediately when
    // started from the request handler right after the mode switch, which made
    // the handover give up without ever attempting a connection. Blocking here
    // stalls the loop for a second or two -- during setup there is no radio
    // link and no audio to disturb, and the portal page tolerates a lost poll.
    int found = WiFi.scanNetworks(false, false, false, 150);
    wifiTryCandidateCount = (found > 0) ? collectVisibleWifiProfiles(found, wifiTryCandidates) : 0;
    WiFi.scanDelete();
    wifiTryScanSawNothing = (found >= 0 && wifiTryCandidateCount == 0);

    if (wifiTryCandidateCount == 0) {
      // A scan that saw nothing is not proof of absence: it may have failed
      // outright, and a hidden SSID never appears in one. Try the credentials
      // anyway rather than refusing on the strength of a negative.
      Serial.print("WIFI| AP handoff: scan found no configured SSID (");
      Serial.print(found);
      Serial.println(" APs), trying every profile blind");
      wifiTryCandidateCount = fillBlindWifiCandidates(wifiTryCandidates);
    }
    if (wifiTryCandidateCount == 0) {
      wifiTryFail("no_ssid");
      return;
    }
    wifiTryCandidateIdx = 0;
    wifiTryBeginCandidate();
    return;
  }

  if (wifiTryState != WTRY_CONNECTING) return;

  if (WiFi.status() == WL_CONNECTED && (uint32_t)WiFi.localIP() != 0) {
    saveLastStaIp(WiFi.localIP());
    wifiTryState = WTRY_OK;
    Serial.print("WIFI| AP handoff: station up at ");
    Serial.println(WiFi.localIP());
    return;
  }
  if ((long)(millis() - wifiTryDeadline) >= 0) {
    wifiTryCandidateIdx++;
    if (wifiTryCandidateIdx < wifiTryCandidateCount) {
      Serial.println("WIFI| AP handoff: next configured SSID");
      WiFi.disconnect(false, false);
      wifiTryBeginCandidate();
      return;
    }
    // Every profile was attempted. Whether the scan had seen them decides which
    // of the two useful explanations the operator gets.
    wifiTryFail(wifiTryScanSawNothing ? "not_found" : "no_connect");
  }
}

//-------------------------------------------------------------------------------------------------------
// Remembers the model a radio reported in its capabilities packet. Touches
// flash only on an actual change, which in practice means once per radio.
// The label a slot falls back to when the operator has not typed one. It used to
// be the hardcoded string "IC-705", which was a fair guess while that was the only
// radio this interface spoke to and became a false claim the moment it spoke to
// five. The radio reports its own model and we keep that across reboots, so use
// it; the slot number is the only honest answer when nothing has ever answered.
String defaultTrxLabel(uint8_t slot) {
  if (slot < 3 && radioSlots[slot].model.length() > 0)
    return trimMemoryValue(radioSlots[slot].model, 10);
  return String("TRX") + String(slot + 1);
}

// Adopt a freshly learned model as the label, but only while the label is still a
// bare slot number -- anything else is the operator's own wording and outranks
// what the radio calls itself.
void adoptModelAsLabelIfUnset(uint8_t slot) {
  if (slot >= 3) return;
  String *label = slot == 0 ? &g_lcTrx1Label : slot == 1 ? &g_lcTrx2Label : &g_lcTrx3Label;
  String neutral = String("TRX") + String(slot + 1);
  if (label->length() != 0 && *label != neutral) return;
  String next = defaultTrxLabel(slot);
  if (next == *label) return;
  // In memory only. The model is already persisted in radio-config.json, so this
  // is recomputed on every boot; writing log-config.json here would mean rebuilding
  // the whole document (blockedDxcc and the RST defaults included) to change one
  // display string, and an operator-typed label must keep winning anyway.
  *label = next;
}

void rememberRadioModel(uint8_t slot, const char* model) {
  if (slot >= 3 || !model || !model[0]) return;
  String clean = trimMemoryValue(String(model), 15);
  if (clean.length() == 0 || clean == radioSlots[slot].model) return;
  radioSlots[slot].model = clean;
  Serial.print("CFG | TRX");
  Serial.print(slot + 1);
  Serial.print(" reports model ");
  Serial.println(clean);
  if (!saveRadioConfig()) Serial.println("CFG | radio model save failed");
  adoptModelAsLabelIfUnset(slot);
}

// Picks the model up from an ordinary session too, not just from the SETUP
// test: swapping the radio behind an address has to correct the stored value
// without the operator remembering to press anything.
void radioModelLearnTick() {
  if (APmode) return;
  uint8_t slot = lanRadioSlotIndex();
  if (slot == 0xFF) return;
  IcomLanClient* client = radioLanClient(slot);
  if (!client || !client->connected()) return;
  rememberRadioModel(slot, client->radioModelName());
}

//-------------------------------------------------------------------------------------------------------
// LAN radio discovery + credential test, driven from the main loop.
//
// Both need UDP 50001, which the live client owns, so both go through the same
// stop-then-restore path. Nothing here ever runs a second socket alongside the
// real one: WiFiUDP sets SO_REUSEADDR, so the duplicate bind would succeed and
// then quietly eat the client's control packets instead of failing loudly.
void icomScanStopLanClients() {
  if (icomScanSuspendLan) return;
  icomScanLanWasUp = (lanRadioSlotIndex() != 0xFF);
  lanClient.stop();
  for (uint8_t i = 0; i < 2; i++) if (secondaryLanClients[i]) secondaryLanClients[i]->stop();
  icomScanSuspendLan = true;
}

void icomScanResumeLanClients() {
  if (!icomScanSuspendLan) return;
  icomScanSuspendLan = false;
  lanRetryAt = 0;
  lanBackoff = 3000;
  if (icomScanLanWasUp) lanReconnectRequested = true;
  icomScanLanWasUp = false;
}

void icomScanTick() {
  switch (icomScanPhase) {
    case ISCAN_IDLE:
    case ISCAN_DONE:
      return;

    case ISCAN_SUSPEND:
      icomScanStopLanClients();
      if (!icomScan.start()) {
        icomScanFailed = true;
        icomScanResumeLanClients();
        icomScanPhase = ISCAN_DONE;
        return;
      }
      icomScanPhase = ISCAN_RUN;
      return;

    case ISCAN_RUN:
      icomScan.tick();
      if (icomScan.scanState() == IcomLanDiscovery::DONE) {
        Serial.print("SCAN| finished, ");
        Serial.print(icomScan.count());
        Serial.println(" radio(s) answered on 50001");
        icomScanResumeLanClients();
        icomScanPhase = ISCAN_DONE;
      }
      return;

    case ISCAN_TEST_SUSPEND: {
      icomScanStopLanClients();
      // ~30 kB per client (1500 B scratch + two replay histories), so this is
      // allocated for the test and released again, never kept resident.
      if (!icomTestClient) icomTestClient = new (std::nothrow) IcomLanClient();
      if (!icomTestClient) {
        icomTestResult = "no_answer";
        icomScanResumeLanClients();
        icomScanPhase = ISCAN_DONE;
        return;
      }
      // enableAudio=false keeps openAudioChannel() a no-op, so no audio task is
      // ever spawned and the instance can be deleted the moment we are done.
      icomTestClient->begin(icomTestIp, 50001, icomTestUser.c_str(), icomTestPass.c_str(),
                            icomTestCivAddr, 0, 50001, false);
      icomTestDeadline = millis() + 15000;
      icomScanPhase = ISCAN_TEST_RUN;
      return;
    }

    case ISCAN_TEST_RUN: {
      icomTestClient->loop();
      IcomLanClient::State st = icomTestClient->status();
      // Success is declared at LAN_STREAM -- login, token and auth are all done
      // by then, which is exactly the question the operator asked. Waiting for
      // LAN_CONNECTED would open the CI-V channel and start writing decoded
      // frequency/mode into the shared rig state of a radio we are only probing.
      bool authenticated = (st == IcomLanClient::LAN_STREAM ||
                            st == IcomLanClient::LAN_CIV_AYT ||
                            st == IcomLanClient::LAN_CIV_OPEN ||
                            st == IcomLanClient::LAN_CONNECTED);
      bool finished = false;
      if (authenticated) {
        // LAN_STREAM is only entered after the capabilities packet arrived
        // (maybeRequestStream gates on haveCaps), so the model is guaranteed
        // to be known here -- which is why the test can report and store it.
        icomTestModel = icomTestClient->radioModelName();
        rememberRadioModel(icomTestSlot, icomTestModel.c_str());
        icomTestResult = "ok";
        finished = true;
      } else if (icomTestClient->failed()) {
        icomTestResult = icomTestClient->credentialsRejected() ? "bad_credentials" : "no_answer";
        finished = true;
      } else if ((long)(millis() - icomTestDeadline) >= 0) {
        icomTestResult = "no_answer";
        finished = true;
      }
      if (finished) {
        icomTestClient->stop();     // release the radio's single session at once
        delete icomTestClient;
        icomTestClient = nullptr;
        Serial.print("SCAN| credential test -> ");
        Serial.println(icomTestResult);
        icomScanResumeLanClients();
        icomScanPhase = ISCAN_DONE;
      }
      return;
    }
  }
}

//-------------------------------------------------------------------------------------------------------

void ServiceBackgroundTasks(unsigned long waitMs) {
  unsigned long start = millis();
  while (millis() - start < waitMs) {
    if (trxNetEnabled) net.loop();
    if (APmode) dnsServer.processNextRequest();   // captive portal
    webServer.handleClient();
    #if defined(WDT)
      esp_task_wdt_reset();
    #endif
    delay(10);
  }
}

//-------------------------------------------------------------------------------------------------------
// Must run after WiFi.mode(WIFI_STA) and BEFORE WiFi.begin() -- the hostname is
// only carried in the DHCP request, so setting it later has no effect until the
// next lease. With it the router lists the device as "wifilt" and most consumer
// routers publish that in their local DNS, which is the only find-me path that
// also works from Android (plain unicast DNS, no multicast involved).
//
// setSleep(false) is not cosmetic here: with the default modem power save the AP
// only delivers multicast at DTIM beacons and routinely drops it, which is why
// mDNS answers arrive late or not at all. Costs steady-state current -- revert
// this one line if consumption or heat turns out to matter more than discovery.
void ApplyStaIdentity() {
  WiFi.setHostname(deviceHostname);
  WiFi.setSleep(false);
}

//-------------------------------------------------------------------------------------------------------
void StartMdns() {
  // A failed MDNS.begin() used to park the device in while(1) forever. A name
  // clash or a transient init error is not a reason to brick a radio interface.
  if (!MDNS.begin(deviceHostname)) {
    Serial.println("mDNS| responder failed to start (continuing without it)");
    return;
  }
  MDNS.setInstanceName("IC-705 Interface");
  // _http._tcp is what "find devices on my network" browsers actually look for.
  // It was registered in AP mode only, so on the real LAN nothing could see us.
  MDNS.addService("http", "tcp", 80);
  MDNS.addService("ws", "tcp", 80);
  Serial.print("mDNS| responder started as http://");
  Serial.print(deviceHostname);
  Serial.println(".local");
}

//-------------------------------------------------------------------------------------------------------
// The responder is bound to the interface it was started on; after a reconnect
// the registration is stale and wifilt.local quietly stops resolving -- which is
// most of the "mDNS works sometimes" experience. TrxNet already re-announces on
// this same edge, mDNS was simply forgotten. Kept out of TrxNetLoop() because
// that one returns early when TrxNet is disabled, which is unrelated to mDNS.
void NetworkIdentityLoop() {
  if (APmode) return;
  static bool prevWifiConnected = WiFiStationReady();
  bool wifiConnected = WiFiStationReady();
  if (wifiConnected && !prevWifiConnected) {
    MDNS.end();
    StartMdns();
  }
  prevWifiConnected = wifiConnected;
}

//-------------------------------------------------------------------------------------------------------
bool WiFiStationReady() {
  if (APmode) return true;
  if (WiFi.status() != WL_CONNECTED) return false;
  return (uint32_t)WiFi.localIP() != 0;
}

//-------------------------------------------------------------------------------------------------------
void WiFiRetryActiveProfile(const char *reason, bool hardReset) {
  if (WifiProfileConfigured(ActiveWifiProfile) == false) {
    ActiveWifiProfile = 0;
  }
  String wifiSsid = WifiProfileSSID(ActiveWifiProfile);
  String wifiPswd = WifiProfilePSWD(ActiveWifiProfile);
  bool targeted = !hardReset && wifiLastBssidValid && wifiSsid == wifiLastSsid;
  Serial.print(millis());
  Serial.print(" WIFI| reconnecting ");
  Serial.print(reason);
  if (hardReset) Serial.print(" [radio reset]");
  else if (targeted) { Serial.print(" [bssid ch"); Serial.print(wifiLastChannel); Serial.print("]"); }
  Serial.print(" status=");
  Serial.print((int)WiFi.status());
  Serial.print(" ip=");
  Serial.print(WiFi.localIP());
  Serial.print(" ssid ");
  Serial.println(wifiSsid);
  if (hardReset) {
    // full radio off/on clears wedged driver state, then full-scan connect
    WiFi.disconnect(true, false);
    delay(200);
    WiFi.mode(WIFI_STA);
    delay(100);
    ApplyStaIdentity();
    WiFi.begin(wifiSsid.c_str(), wifiPswd.c_str());
  } else {
    WiFi.disconnect(false, false);
    delay(100);
    ApplyStaIdentity();
    if (targeted) {
      WiFi.begin(wifiSsid.c_str(), wifiPswd.c_str(), wifiLastChannel, wifiLastBssid);
    } else {
      WiFi.begin(wifiSsid.c_str(), wifiPswd.c_str());
    }
  }
}

//-------------------------------------------------------------------------------------------------------
bool WifiProfileConfigured(byte profile) {
  if (profile == 0) {
    return SSID.length() > 0 && PSWD.length() > 0;
  }
  if (profile == 1) {
    return SSID2.length() > 0 && PSWD2.length() > 0;
  }
  return false;
}

//-------------------------------------------------------------------------------------------------------
String WifiProfileSSID(byte profile) {
  if (profile == 1) {
    return SSID2;
  }
  return SSID;
}

//-------------------------------------------------------------------------------------------------------
String WifiProfilePSWD(byte profile) {
  if (profile == 1) {
    return PSWD2;
  }
  return PSWD;
}

//-------------------------------------------------------------------------------------------------------
byte NextWifiProfile(byte profile) {
  if (profile == 0 && WifiProfileConfigured(1)) {
    return 1;
  }
  return 0;
}

//-------------------------------------------------------------------------------------------------------
bool ConnectWiFiProfile(byte profile, int maxTryCount) {
  if (WifiProfileConfigured(profile) == false) {
    return false;
  }

  String wifiSsid = WifiProfileSSID(profile);
  String wifiPswd = WifiProfilePSWD(profile);

  WiFi.disconnect(false, false);
  delay(100);
  ApplyStaIdentity();
  WiFi.begin(wifiSsid.c_str(), wifiPswd.c_str());
  Serial.print("WIFI| Connecting ssid ");
  Serial.print(wifiSsid);
  Serial.print(" ");

  for (int count_try = 0; count_try < maxTryCount; count_try++) {
    if (WiFiStationReady()) {
      Serial.println();
      ActiveWifiProfile = profile;
      return true;
    }
    delay(500);
    Serial.print(".");
  }

  Serial.println();
  print_wifi_error();
  return WiFiStationReady();
}

//-------------------------------------------------------------------------------------------------------
void FallbackToAPmode() {
  APmode = true;
  EEPROM.writeBool(0, true);
  EEPROM.commit();
  delay(500);
  ESP.restart();
}

//-------------------------------------------------------------------------------------------------------
// Matches a finished scan against both configured profiles, strongest AP first.
// Reads scan results only -- the caller owns starting the scan and deleting it.
//
// Choosing by what is actually on the air matters more than it looks: starting
// with profile 0 because it happens to be first costs a full connect timeout
// before the alternation ever reaches the profile that was in range all along.
uint8_t collectVisibleWifiProfiles(int found, WifiScanPick out[2]) {
  uint8_t count = 0;
  for (byte p = 0; p < 2; p++) {
    if (!WifiProfileConfigured(p)) continue;
    String want = WifiProfileSSID(p);
    int best = -1;
    int32_t bestRssi = -127;
    for (int i = 0; i < found; i++) {
      if (WiFi.SSID(i) != want) continue;
      int32_t rssi = WiFi.RSSI(i);
      if (best >= 0 && rssi <= bestRssi) continue;   // same SSID, weaker AP
      best = i;
      bestRssi = rssi;
    }
    if (best < 0) continue;
    out[count].profile = p;
    out[count].rssi = bestRssi;
    out[count].channel = WiFi.channel(best);
    const uint8_t* bssid = WiFi.BSSID(best);
    if (bssid) memcpy(out[count].bssid, bssid, 6);
    count++;
  }
  if (count == 2 && out[1].rssi > out[0].rssi) {
    WifiScanPick swap = out[0];
    out[0] = out[1];
    out[1] = swap;
  }
  return count;
}

void ConnectWiFiAlternating() {
  WiFi.mode(WIFI_STA);

  if (WifiProfileConfigured(0) == false && WifiProfileConfigured(1) == false) {
    Serial.println("WIFI| no configured SSID, staying in AP mode");
    FallbackToAPmode();
  }

  // Scan before connecting — avoids infinite loop when SSIDs are configured but not in range
  Serial.println("WIFI| scanning for configured networks...");
  int n = WiFi.scanNetworks();
  WifiScanPick visible[2];
  uint8_t visibleCount = collectVisibleWifiProfiles(n, visible);
  WiFi.scanDelete();

  if (visibleCount == 0) {
    Serial.println("WIFI| no configured SSID found in scan, switching to AP mode");
    FallbackToAPmode();
  }

  // Start with the profile the scan actually saw, strongest first, instead of
  // always profile 0. The alternation below still covers the other one.
  byte wifiProfile = visible[0].profile;
  Serial.print("WIFI| ");
  Serial.print(WifiProfileSSID(wifiProfile));
  Serial.print(" visible at ");
  Serial.print(visible[0].rssi);
  Serial.println(" dBm, trying it first");

  WifiTimer = millis();
  int attempts = 0;
  const int maxAttempts = 4;
  while (!WiFiStationReady()) {
    if (ConnectWiFiProfile(wifiProfile, wifi_max_try)) {
      break;
    }
    attempts++;
    if (attempts >= maxAttempts) {
      Serial.println("WIFI| max retries reached, switching to AP mode");
      FallbackToAPmode();
    }
    Serial.println("WIFI| switching to next configured SSID");
    wifiProfile = NextWifiProfile(wifiProfile);
  }
}

//-------------------------------------------------------------------------------------------------------

String IntToTenString(int NR) {
  String str = String(NR);
  while (str.length() < 10) {
    str = "0" + str;
  }
  return str;
}

//-------------------------------------------------------------------------------------------------------
void SplitString(String ORIGINAL, String* SplitStrFreq) {
  for (int i = 0; i < 5; i++) {
    SplitStrFreq[i] = ORIGINAL.substring(i * 2, i * 2 + 2);
    // Serial.println(SplitStrFreq[i]);
  }
}

//-------------------------------------------------------------------------------------------------------

byte stringToByte(String str) {
  // Převod prvního znaku na číslo
  byte prvniZnak = str.charAt(0) - '0';

  // Převod druhého znaku na číslo a posun do vyššího číselného řádu
  byte druhyZnak = str.charAt(1) - '0';

  // Sestavení výsledné hodnoty
  byte vysledek = (prvniZnak << 4) | druhyZnak;

  return vysledek;
}

//-------------------------------------------------------------------------------------------------------
// uint32_t readADC_Cal(int ADC_Raw)
// {
//   esp_adc_cal_characteristics_t adc_chars;

//   esp_adc_cal_characterize(ADC_UNIT_1, ADC_ATTEN_DB_11, ADC_WIDTH_BIT_12, 1100, &adc_chars);
//   return(esp_adc_cal_raw_to_voltage(ADC_Raw, &adc_chars));
// }

//-------------------------------------------------------------------------------------------------------
void print_wifi_error(){
  switch(WiFi.status())
  {
    case WL_IDLE_STATUS : Serial.println("WiFi| WL_IDLE_STATUS"); break;
    case WL_NO_SSID_AVAIL : Serial.println("WiFi| WL_NO_SSID_AVAIL"); break;
    case WL_CONNECT_FAILED : Serial.println("WiFi| WL_CONNECT_FAILED"); break;
    case WL_DISCONNECTED : Serial.println("WiFi| WL_DISCONNECTED"); break;
    default : Serial.printf("WiFi| No know WiFi error"); break;
  }
}
//-------------------------------------------------------------------------------------------------------
// void processCatMessages(){
//   #if defined(BLUETOOTH)
//     /*
//       <FE FE E0 42 04 00 01 FD  - LSB
//       <FE FE E0 42 03 00 00 58 45 01 FD  -145.580.000

//       FE FE - start bytes
//       00/E0 - target address (broadcast/controller)
//       42 - source address
//       00/03 - data type
//       <data>
//       FD - stop byte
//     */

//     while (CAT.available()) {
//       uint8_t knowncommand = 1;
//       uint8_t r;
//       if (readLine() > 0) {
//         if (read_buffer[0] == START_BYTE && read_buffer[1] == START_BYTE) {
//           if (read_buffer[3] == radio_address) {
//             if (read_buffer[2] == BROADCAST_ADDRESS) {
//               switch (read_buffer[4]) {
//                 case CMD_TRANS_FREQ:
//                   printFrequency();
//                   break;
//                 case CMD_TRANS_MODE:
//                   printMode();
//                   break;
//                 default:
//                   knowncommand = false;
//               }
//             } else if (read_buffer[2] == CONTROLLER_ADDRESS) {
//               switch (read_buffer[4]) {
//                 case CMD_READ_FREQ:
//                   printFrequency();
//                   break;
//                 case CMD_READ_MODE:
//                   printMode();
//                   break;
//                 default:
//                   knowncommand = false;
//               }
//             }
//           } else {
//             // if(Debug==true){
//             //   Serial.print(read_buffer[3]);
//             //   Serial.println(" also on-line?!");
//             // }
//           }
//         }
//         powerTimer=millis(); // RX BT

//       }
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
