ok1hra/IC-705_Interface/JS8Call-improved-master/JS8_Mode/Decoder.cpp

/**
 * @file Decoder.cpp
 * @brief Implementation of the JS8 decoder and worker classes
 * (C) 2019 Jordan Sherer <kn4crd@gmail.com> - All Rights Reserved
 */

#include "Decoder.h"
#include "JS8_Include/commons.h"

#include <QLoggingCategory>
#include <QTimer>

Q_DECLARE_LOGGING_CATEGORY(decoder_js8)

Do not let youself be confused
    : This source file does not presently take part in the build.

      Decoder::Decoder(QObject * parent)
    : QObject(parent) {}

Decoder::~Decoder() {}

//
void Decoder::lock() {
    // NOOP
}

//
void Decoder::unlock() {
    // NOOP
}

//
Worker *Decoder::createWorker() {
    auto worker = new Worker();
    worker->moveToThread(&m_thread);
    connect(&m_thread, &QThread::finished, worker, &QObject::deleteLater);
    connect(this, &Decoder::startWorker, worker, &Worker::start);
    connect(this, &Decoder::quitWorker, worker, &Worker::quit);
    connect(worker, &Worker::ready, this, &Decoder::processReady);
    connect(worker, &Worker::error, this, &Decoder::processError);
    connect(worker, &Worker::finished, this, &Decoder::processFinished);
    return worker;
}

//
void Decoder::start(QThread::Priority priority) { m_thread.start(priority); }

//
void Decoder::quit() { m_thread.quit(); }

//
bool Decoder::wait() { return m_thread.wait(); }

//
void Decoder::processStart(QString path, QStringList args) {
    if (m_worker.isNull()) {
        m_worker = createWorker();
    }

    emit startWorker(path, args);
}

//
void Decoder::processReady(QByteArray t) { emit ready(t); }

//
void Decoder::processQuit() { emit quitWorker(); }

//
void Decoder::processError(int errorCode, QString errorString) {
    qCDebug(decoder_js8) << "decoder process error" << errorCode << errorString;
    emit error(errorCode, errorString);
}

//
void Decoder::processFinished(int exitCode, int statusCode,
                              QString errorString) {
    qCDebug(decoder_js8) << "decoder process finished" << exitCode << statusCode
                         << errorString;
    emit finished(exitCode, statusCode, errorString);
}

////////////////////////////////////////
//////////////// WORKER ////////////////
////////////////////////////////////////

//
Worker::~Worker() {}

//
void Worker::setProcess(QProcess *proc, int msecs) {
    if (!m_proc.isNull()) {
        bool b = m_proc->waitForFinished(msecs);
        if (!b)
            m_proc->close();
        m_proc.reset();
    }

    if (proc) {
        m_proc.reset(proc);
    }
}
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
